geoffrey-young/3D-Printing/models/creality/ender-3-v2/z-drive-helpers/images/IMG_3741.jpg

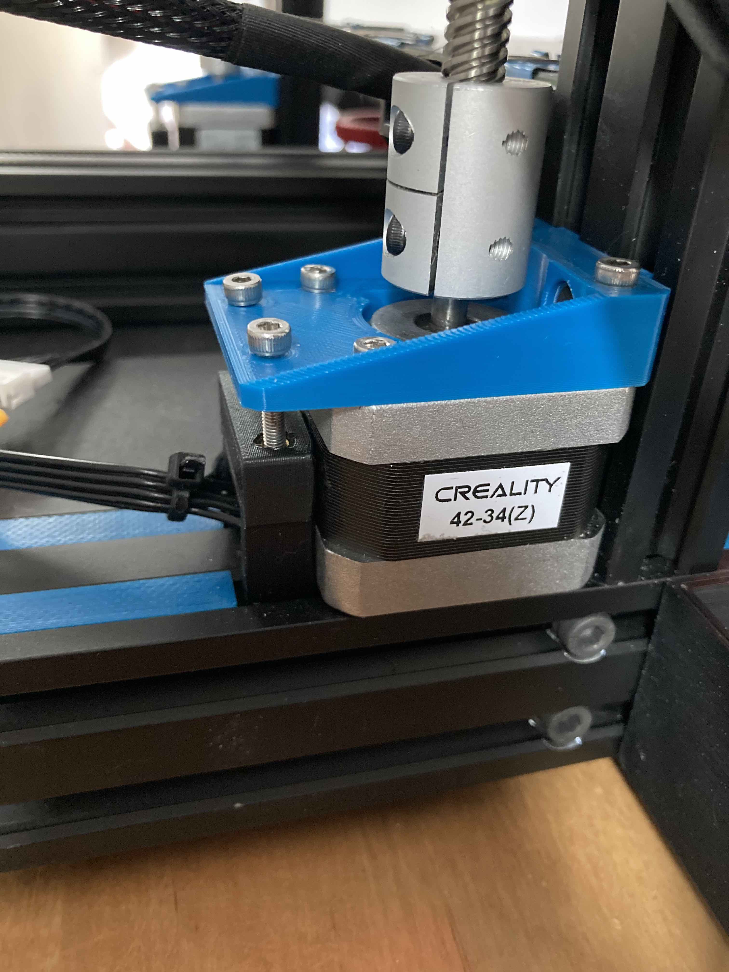
models/creality/ender-3-v2/z-drive-helpers/images/IMG_3741.jpg
