geoffrey-young/3D-Printing/models/creality/ender-3-v2/z-drive-helpers/images/motor.jpg

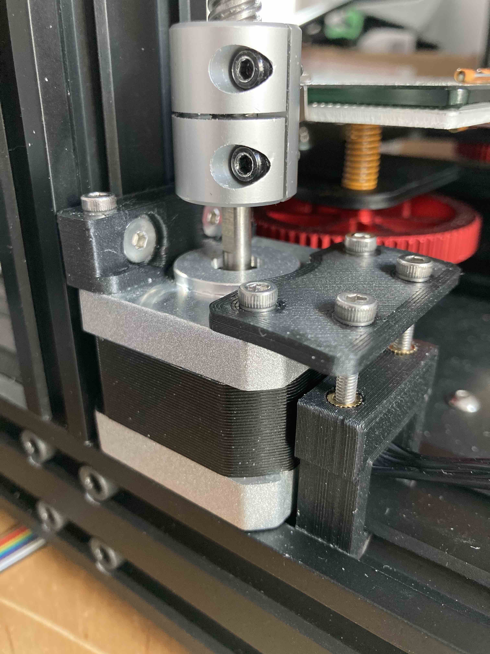
models/creality/ender-3-v2/z-drive-helpers/images/motor.jpg
