geoffrey-young/3D-Printing/models/d20-wall-art/images/IMG_3674.jpg

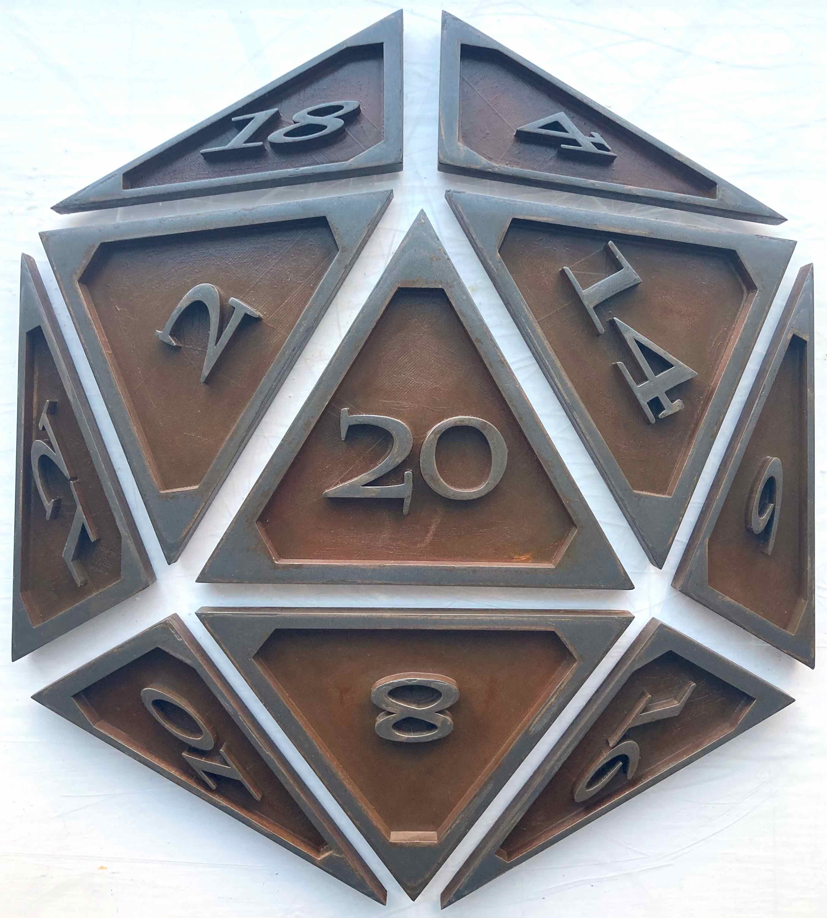
models/d20-wall-art/images/IMG_3674.jpg
