geoffrey-young/3D-Printing/models/d20-wall-art/images/IMG_6126.JPG

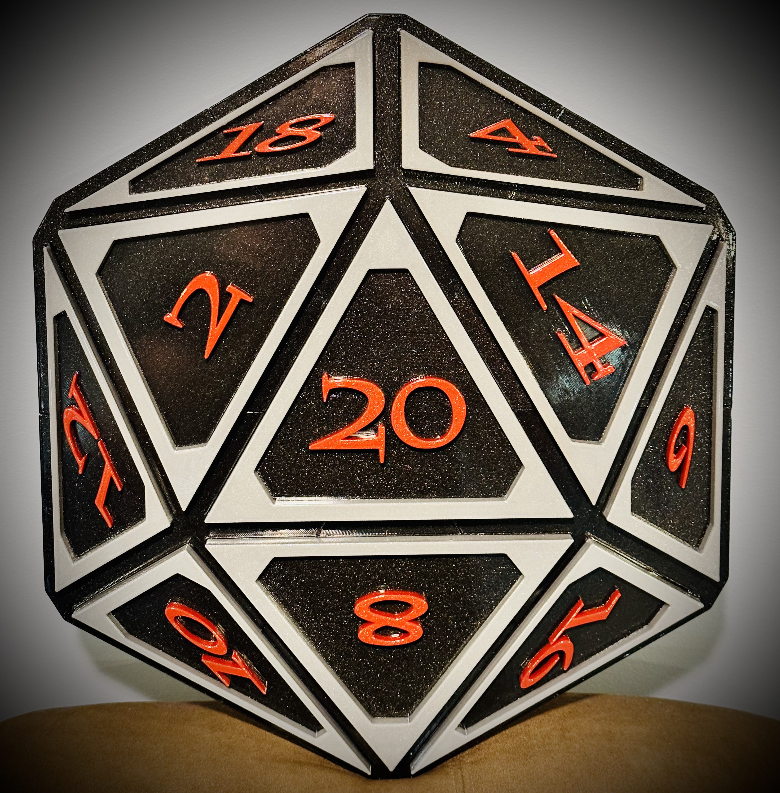
models/d20-wall-art/images/IMG_6126.JPG
