geoffrey-young/3D-Printing/models/voron/2.4/stl/spool-holder/spool-holder.png

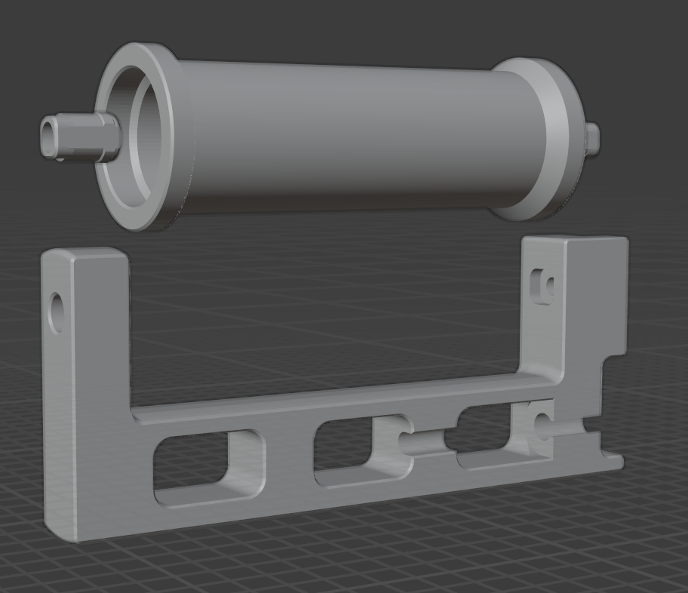
models/voron/2.4/stl/spool-holder/spool-holder.png
