geoffrey-young/3D-Printing/superslicer/voron/sw/ender3_glassbed.png

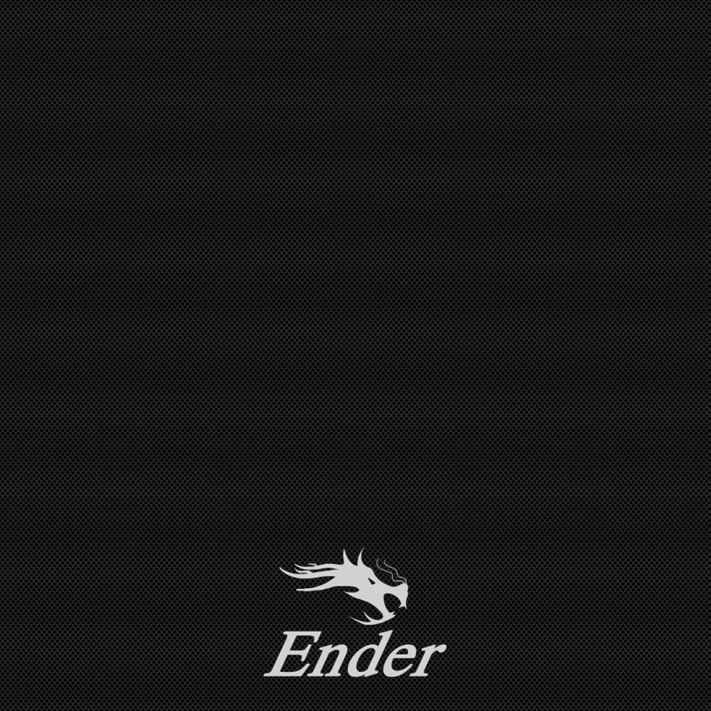
superslicer/voron/sw/ender3_glassbed.png
