geoffrey-young/3D-Printing/models/voron/enderwire/stl/new/y-axis-adxl-mount.stl

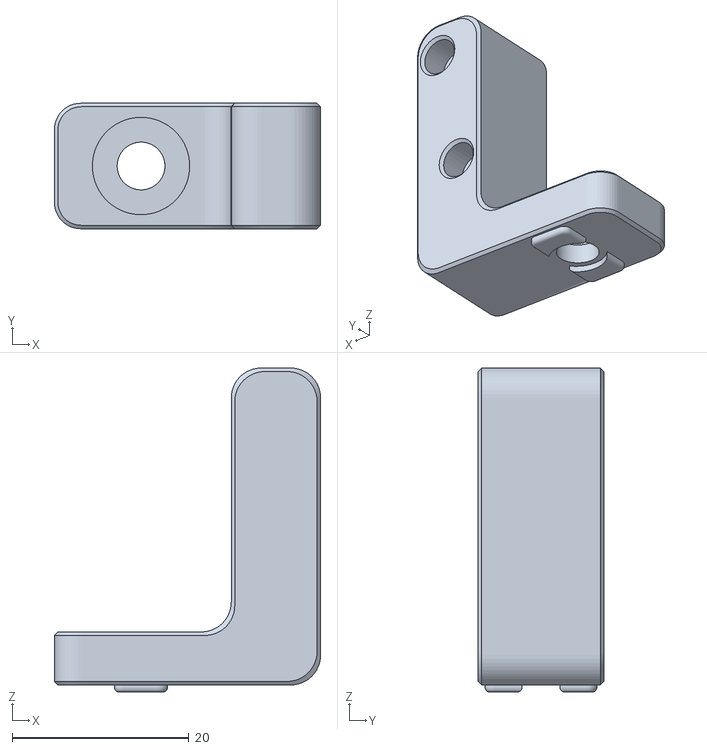
[picture p56: CAD file, 2025-04-14]
models/voron/enderwire/stl/new/y-axis-adxl-mount.stl
30.1 x 14.2 x 36.6
