geoffrey-young/3D-Printing/models/voron/enderwire/stl/replacements/keybak_mount.stl

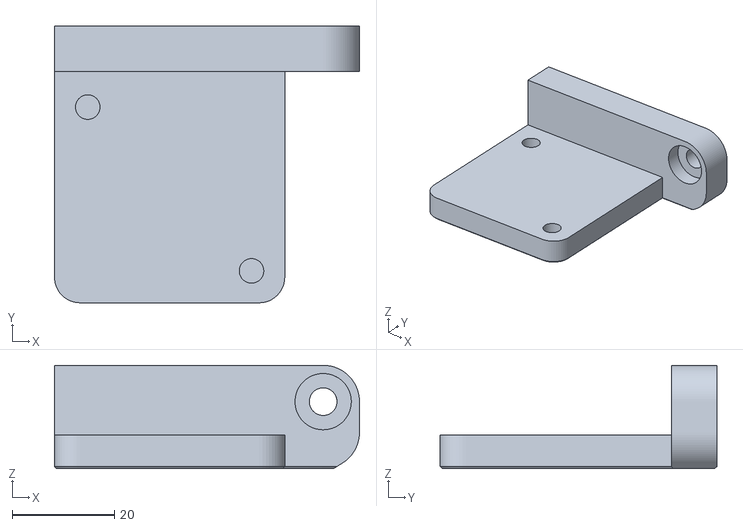
[picture p57: CAD file, 2022-06-13]
models/voron/enderwire/stl/replacements/keybak_mount.stl
59.6 x 54.1 x 20.2
