geoffrey-young/3D-Printing/models/voron/ercf/extender/stl/[a]_10mm-ecas-to-magnet-end_xN.stl

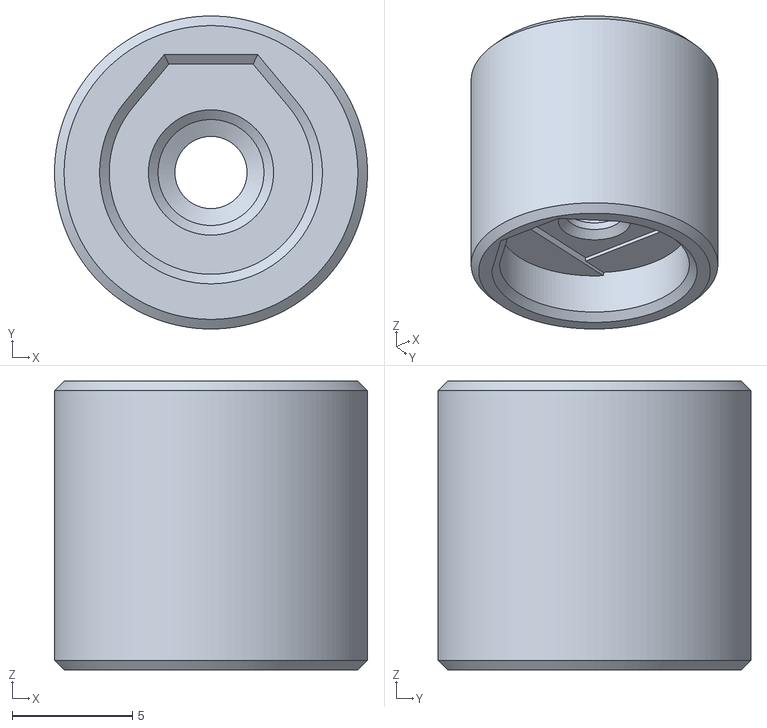
[picture p58: CAD file, 2023-09-01]
models/voron/ercf/extender/stl/[a]_10mm-ecas-to-magnet-end_xN.stl
13.0 x 13.0 x 12.0
