geoffrey-young/3D-Printing/models/voron/ercf/mounts/bridge/stl/bridge-mount-9.stl

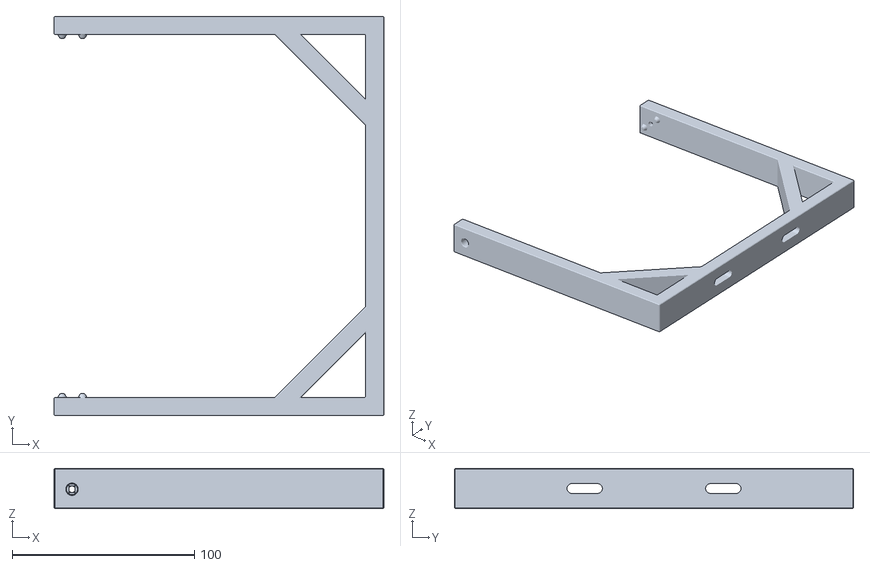
[picture p59: CAD file, 2023-04-11]
models/voron/ercf/mounts/bridge/stl/bridge-mount-9.stl
180.8 x 218.8 x 22.0
