geoffrey-young/3D-Printing/models/voron/ercf/mounts/ercf-french-cleat/stl/frame-6.stl

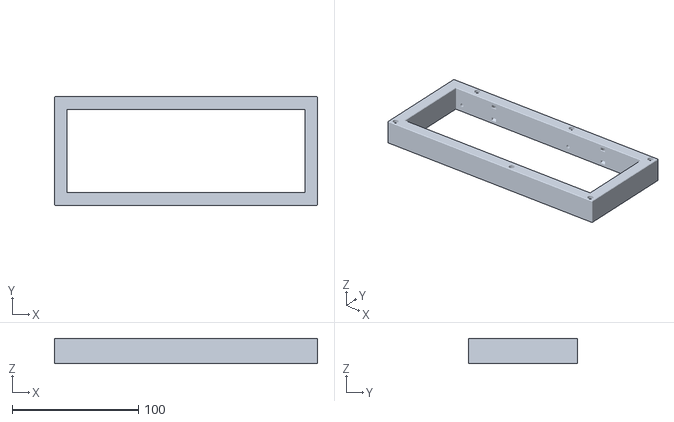
[picture p60: CAD file, 2023-05-19]
models/voron/ercf/mounts/ercf-french-cleat/stl/frame-6.stl
208.0 x 86.0 x 20.0
