geoffrey-young/3D-Printing/models/voron/ercf/random/half-hotends/half-rapido-multicolor.stl

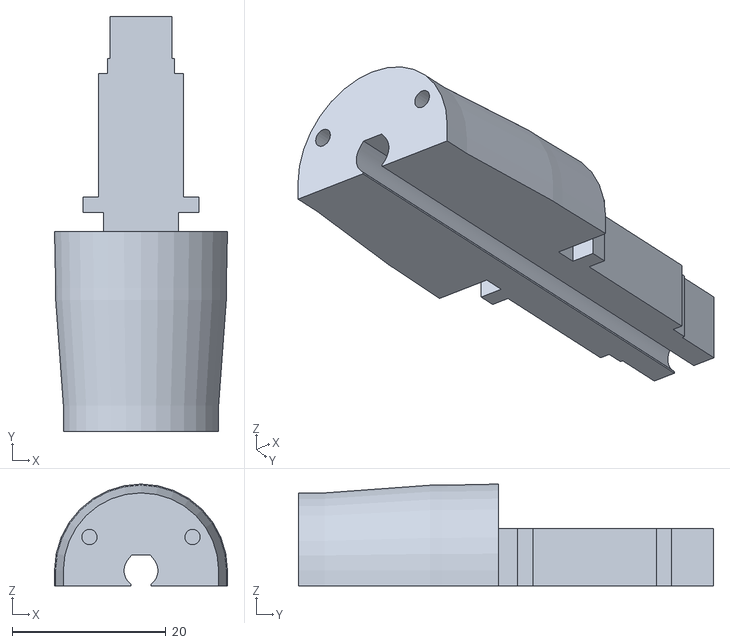
[picture p61: CAD file, 2023-09-01]
models/voron/ercf/random/half-hotends/half-rapido-multicolor.stl
22.5 x 54.0 x 13.3
