geoffrey-young/3D-Printing/models/voron/stealthburner/stl/lgx/cw1/sb-lgx-rear-cw1.stl

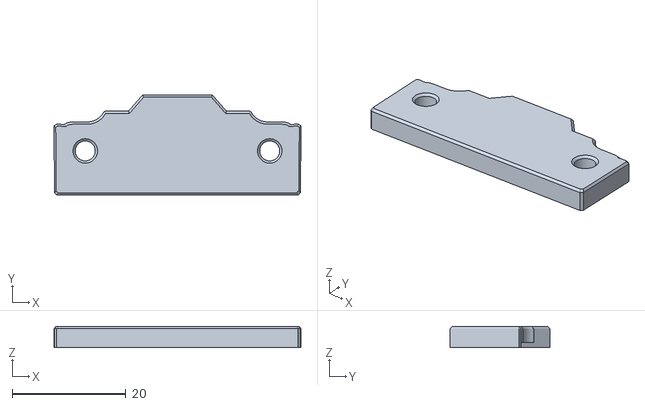
[picture p63: CAD file, 2022-05-10]
models/voron/stealthburner/stl/lgx/cw1/sb-lgx-rear-cw1.stl
43.4 x 17.6 x 3.70
