geoffrey-young/3D-Printing/models/voron/stealthburner/stl/lgx/cw2/sb-lgx-cw2-ercf-v5.stl

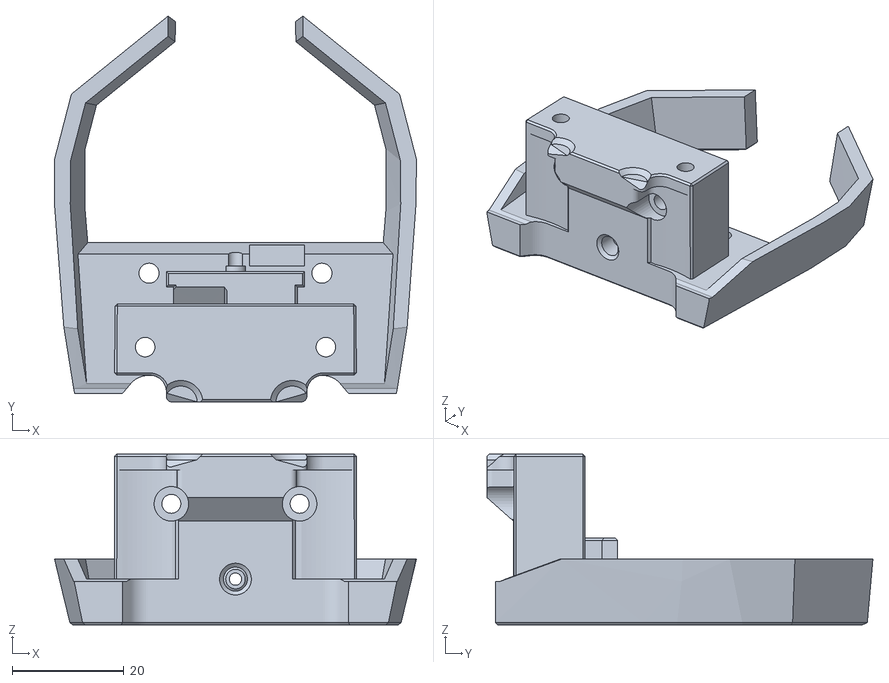
[picture p64: CAD file, 2022-11-18]
models/voron/stealthburner/stl/lgx/cw2/sb-lgx-cw2-ercf-v5.stl
64.9 x 69.2 x 30.6
