geoffrey-young/3D-Printing/models/voron/stealthburner/stl/lgx/sb-lgx-anchor.stl

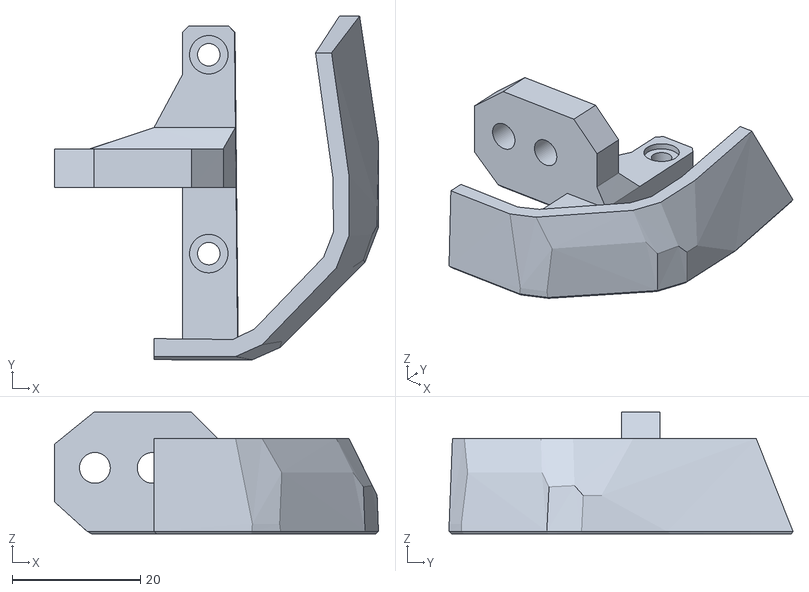
[picture p65: CAD file, 2023-06-22]
models/voron/stealthburner/stl/lgx/sb-lgx-anchor.stl
50.5 x 53.6 x 19.0
