geoffrey-young/3D-Printing/models/voron/stealthburner/stl/sb-official-rapido_filled.stl

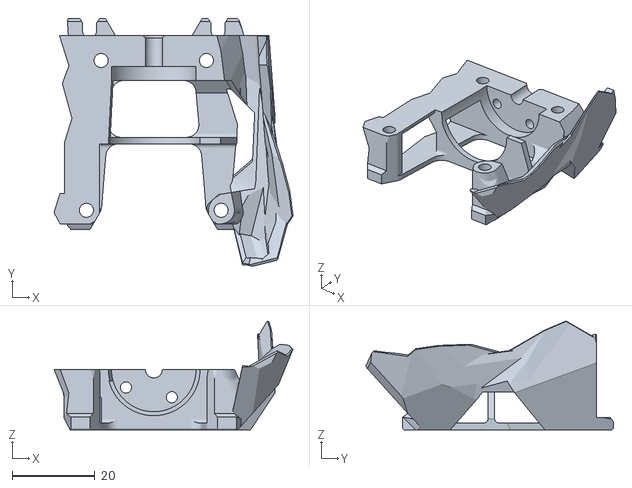
[picture p66: CAD file, 2025-04-14]
models/voron/stealthburner/stl/sb-official-rapido_filled.stl
57.7 x 59.7 x 26.3
