geoffrey-young/3D-Printing/models/voron/tap/r8/short-thick-tap-belt-cover.stl

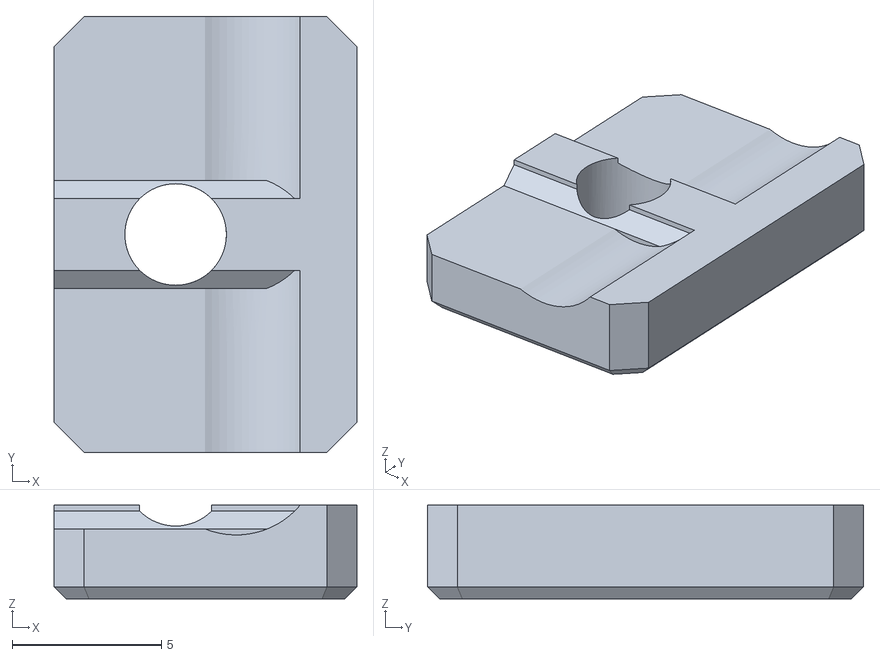
[picture p67: CAD file, 2023-06-17]
models/voron/tap/r8/short-thick-tap-belt-cover.stl
10.1 x 14.6 x 3.14
