geoffrey-young/3D-Printing/models/d20-wall-art/v2/v2-4.stl

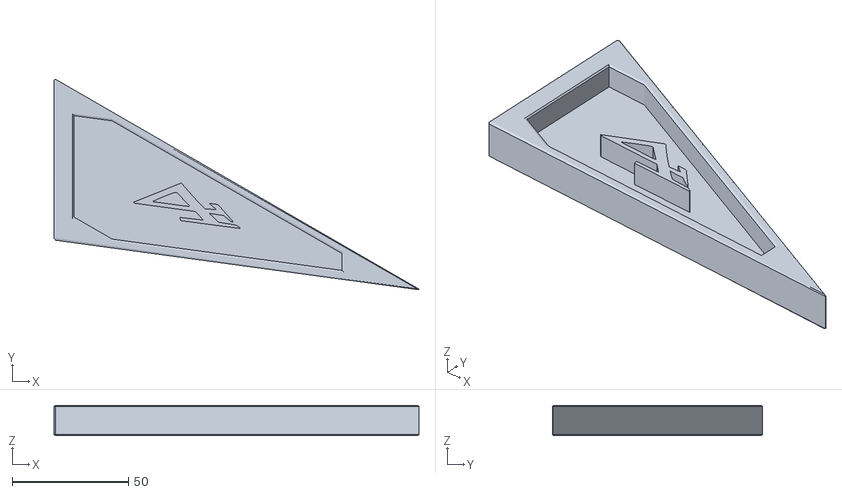
[picture p69: CAD file, 2023-04-01]
models/d20-wall-art/v2/v2-4.stl
157.1 x 90.6 x 13.0
