geoffrey-young/3D-Printing/models/voron/2.4/stl/bofa/filter_access_cover.stl

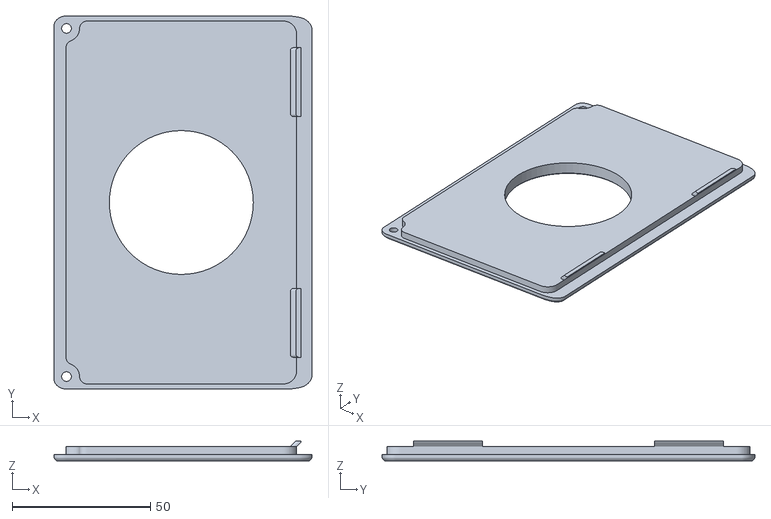
[picture p70: CAD file, 2021-09-11]
models/voron/2.4/stl/bofa/filter_access_cover.stl
93.2 x 134.8 x 7.20
