geoffrey-young/3D-Printing/models/voron/2.4/stl/chains/chain-hold.stl

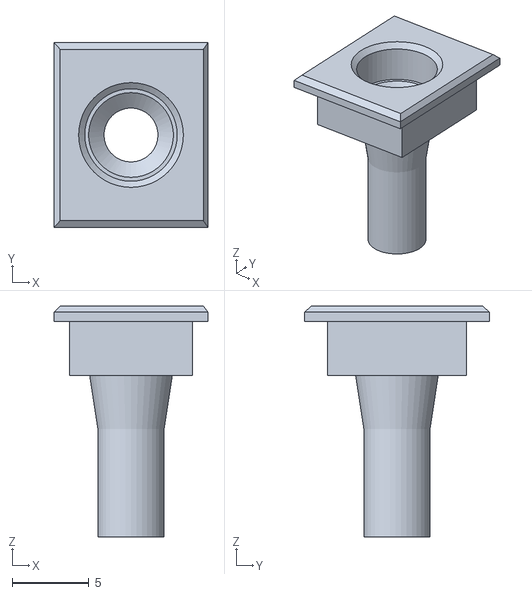
[picture p71: CAD file, 2023-05-01]
models/voron/2.4/stl/chains/chain-hold.stl
10.0 x 12.0 x 15.0
