geoffrey-young/3D-Printing/models/voron/2.4/stl/doors/door_handle_guide.stl

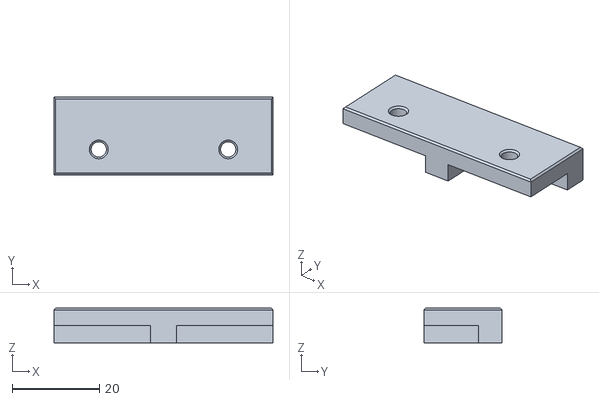
[picture p72: CAD file, 2023-05-01]
models/voron/2.4/stl/doors/door_handle_guide.stl
50.2 x 17.8 x 8.00
