geoffrey-young/3D-Printing/models/voron/2.4/stl/ge5c/ge5c_4_0mm_wider_y_endstop.stl

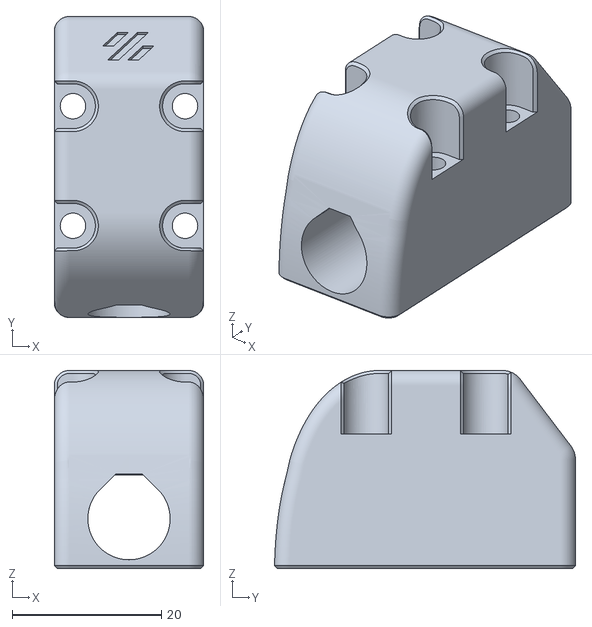
[picture p73: CAD file, 2023-05-01]
models/voron/2.4/stl/ge5c/ge5c_4_0mm_wider_y_endstop.stl
20.0 x 40.3 x 26.5
