geoffrey-young/3D-Printing/models/voron/2.4/stl/other/xy-jst-endstop-pod.stl

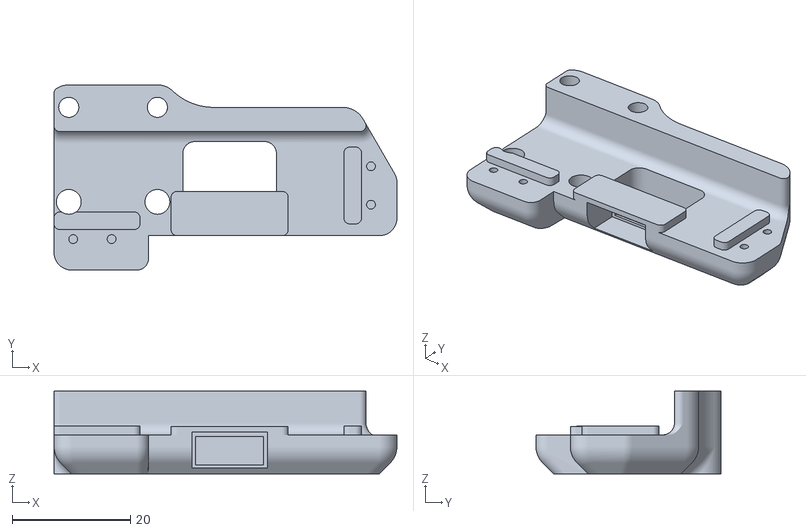
[picture p74: CAD file, 2023-05-01]
models/voron/2.4/stl/other/xy-jst-endstop-pod.stl
58.0 x 31.4 x 14.0
