geoffrey-young/3D-Printing/models/voron/2.4/stl/sb-lgx/lgx-lever-cover.stl

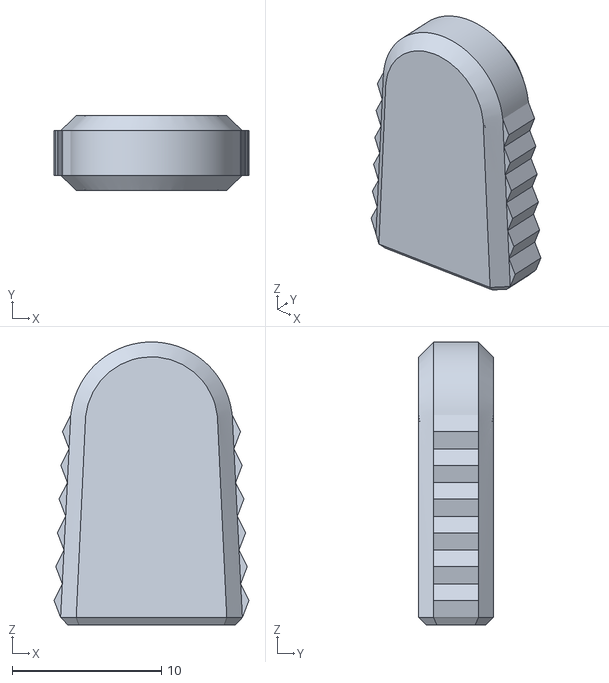
[picture p75: CAD file, 2021-06-12]
models/voron/2.4/stl/sb-lgx/lgx-lever-cover.stl
13.1 x 5.00 x 19.0
