geoffrey-young/3D-Printing/models/voron/2.4/stl/skirts/left-rear.stl

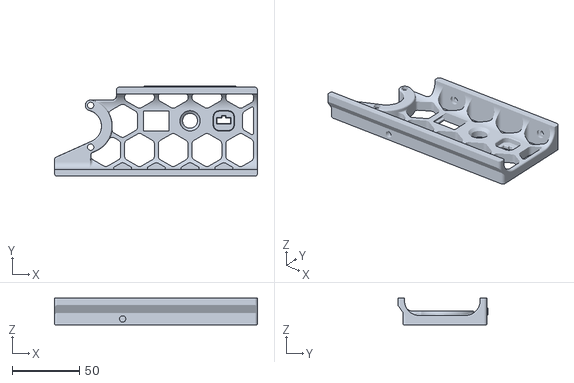
[picture p76: CAD file, 2023-05-01]
models/voron/2.4/stl/skirts/left-rear.stl
150.5 x 67.0 x 20.0
