geoffrey-young/3D-Printing/models/voron/2.4/stl/spool-holder/bearing_mount-x2.stl

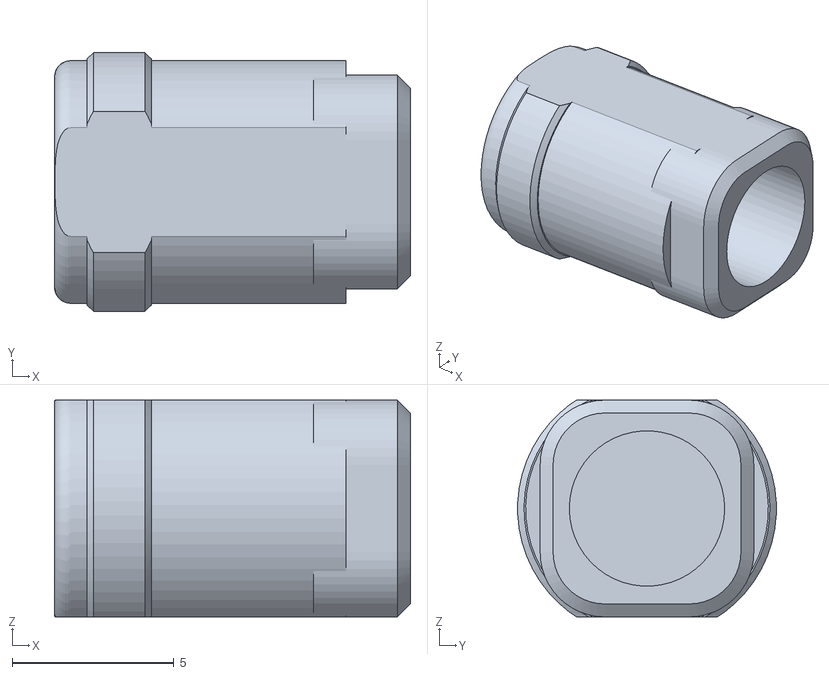
[picture p77: CAD file, 2021-06-15]
models/voron/2.4/stl/spool-holder/bearing_mount-x2.stl
11.0 x 7.99 x 6.70
