geoffrey-young/3D-Printing/models/voron/2.4/stl/tap/55mm-a__Tap_Center_r8.stl

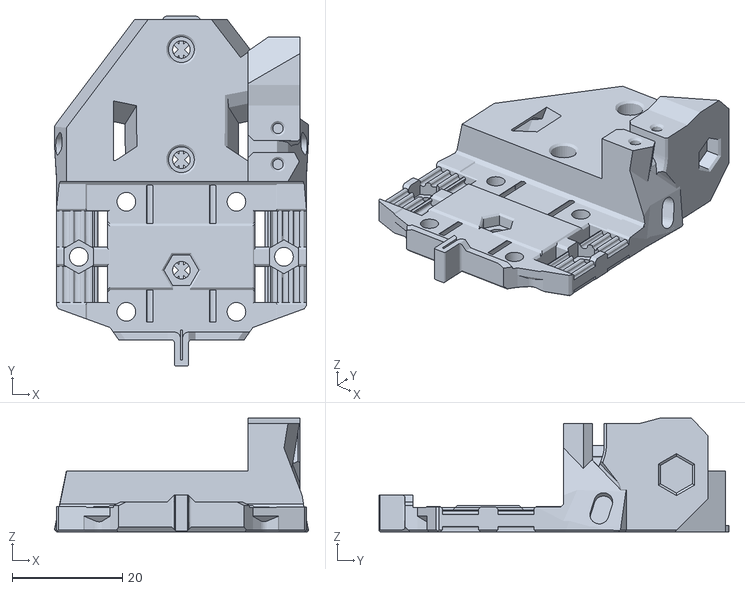
[picture p78: CAD file, 2023-06-17]
models/voron/2.4/stl/tap/55mm-a__Tap_Center_r8.stl
46.2 x 63.6 x 20.7
