geoffrey-young/3D-Printing/models/voron/enderwire/stl/new/long-klicky-mount.stl

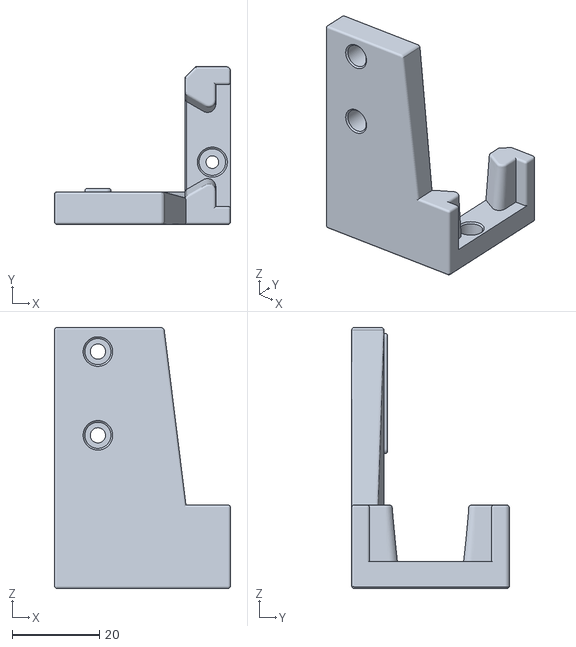
[picture p79: CAD file, 2023-12-30]
models/voron/enderwire/stl/new/long-klicky-mount.stl
40.5 x 36.3 x 60.0
