geoffrey-young/3D-Printing/models/voron/enderwire/stl/replacements/[a]_y_axis_ls_mount.stl

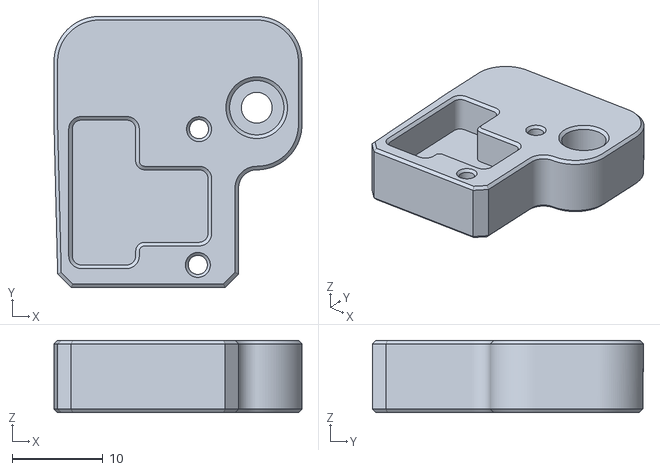
[picture p80: CAD file, 2022-06-13]
models/voron/enderwire/stl/replacements/[a]_y_axis_ls_mount.stl
27.4 x 30.0 x 8.00
