geoffrey-young/3D-Printing/models/voron/ercf/extender/stl/10mm-extender-6.stl

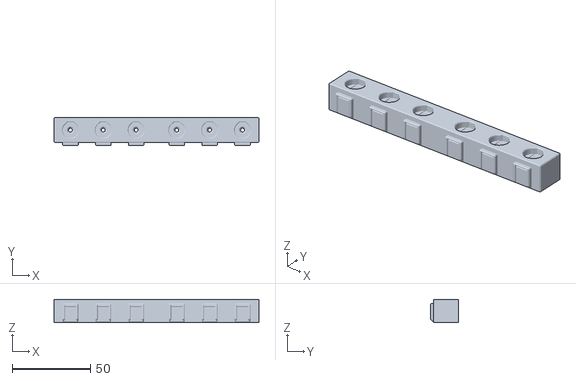
[picture p81: CAD file, 2023-09-01]
models/voron/ercf/extender/stl/10mm-extender-6.stl
131.0 x 18.0 x 15.0
