geoffrey-young/3D-Printing/models/voron/ercf/mounts/bridge/stl/bridge-9.stl

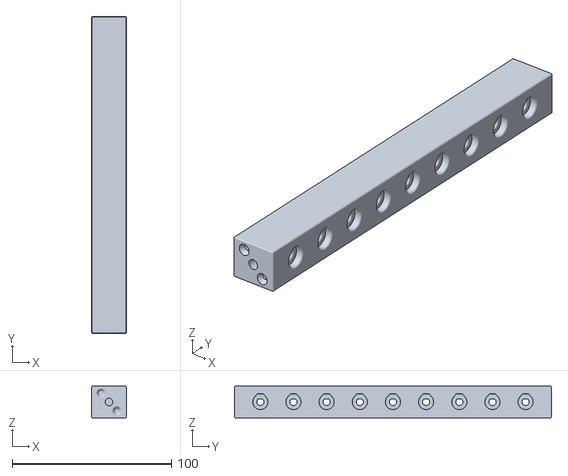
[picture p82: CAD file, 2023-04-11]
models/voron/ercf/mounts/bridge/stl/bridge-9.stl
22.0 x 198.8 x 20.0
