geoffrey-young/3D-Printing/models/voron/ercf/mounts/ercf-french-cleat/stl/wall-mount-6.stl

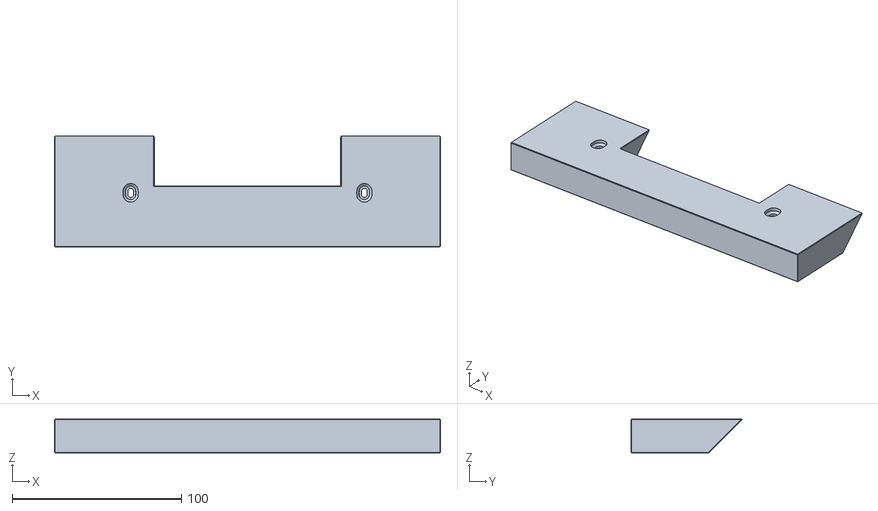
[picture p83: CAD file, 2023-05-19]
models/voron/ercf/mounts/ercf-french-cleat/stl/wall-mount-6.stl
228.0 x 65.7 x 20.0
