geoffrey-young/3D-Printing/models/voron/ercf/random/filament-measure.stl

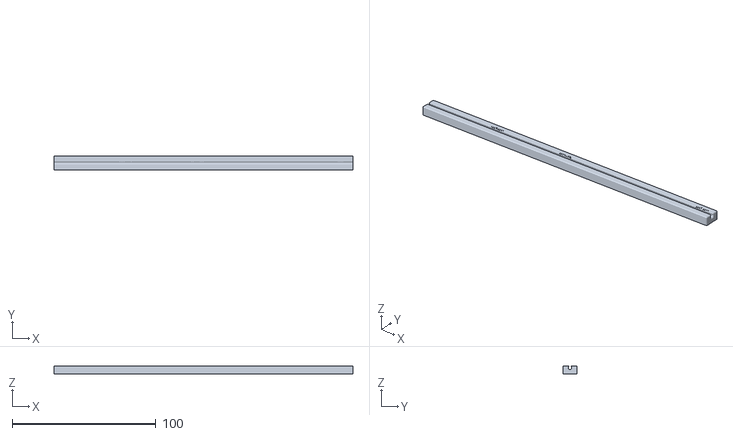
[picture p84: CAD file, 2023-06-12]
models/voron/ercf/random/filament-measure.stl
208.0 x 10.0 x 5.80
