geoffrey-young/3D-Printing/models/voron/ercf/random/half-hotends/half-dragon-multicolor.stl

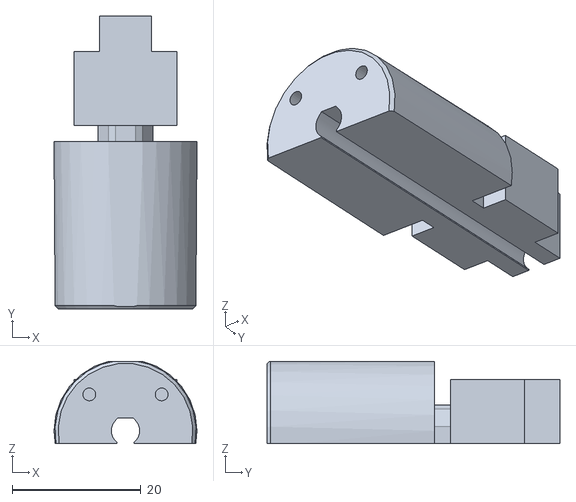
[picture p85: CAD file, 2023-09-01]
models/voron/ercf/random/half-hotends/half-dragon-multicolor.stl
22.2 x 45.5 x 12.8
