geoffrey-young/3D-Printing/models/voron/ercf/upside-down-numbers/stl/3.stl

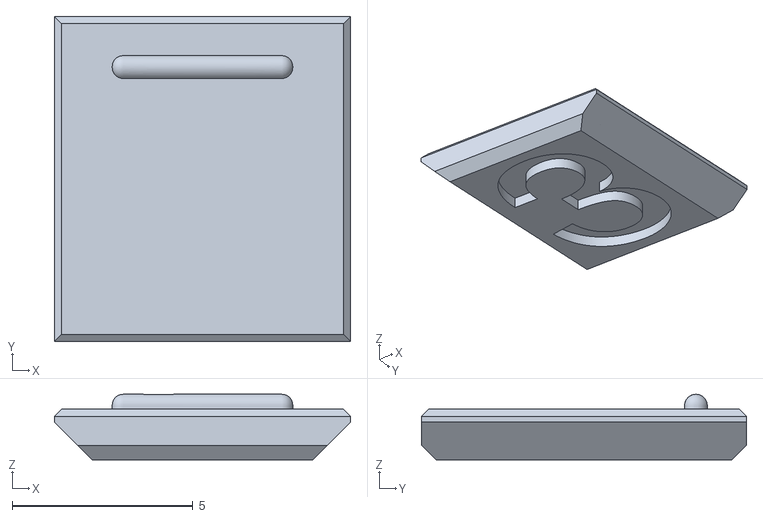
[picture p86: CAD file, 2022-11-07]
models/voron/ercf/upside-down-numbers/stl/3.stl
8.20 x 9.00 x 1.82
