geoffrey-young/3D-Printing/models/voron/stealthburner/stl/lgx/cw1/sb-lgx-front-cw1.stl

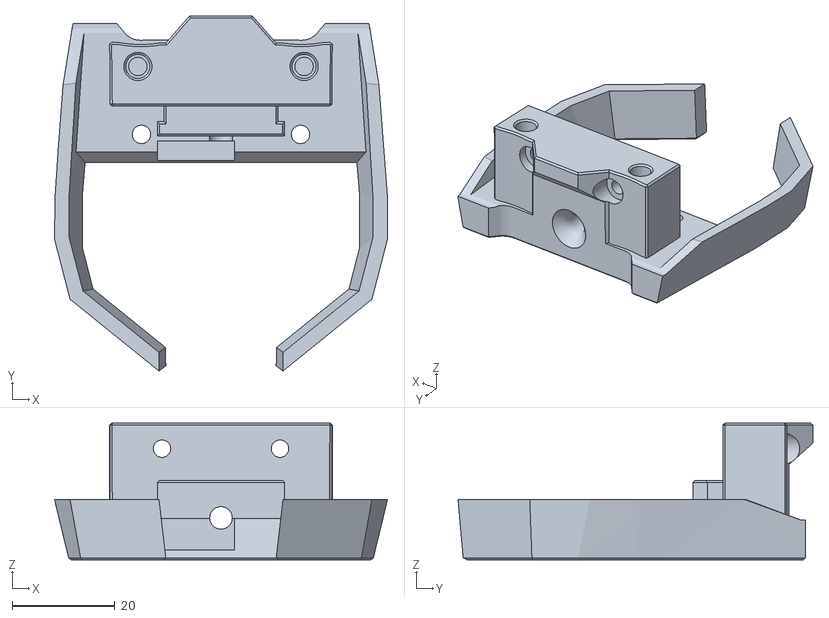
[picture p87: CAD file, 2022-03-18]
models/voron/stealthburner/stl/lgx/cw1/sb-lgx-front-cw1.stl
64.9 x 69.2 x 26.7
