geoffrey-young/3D-Printing/models/voron/stealthburner/stl/lgx/sb-lgx-cover.stl

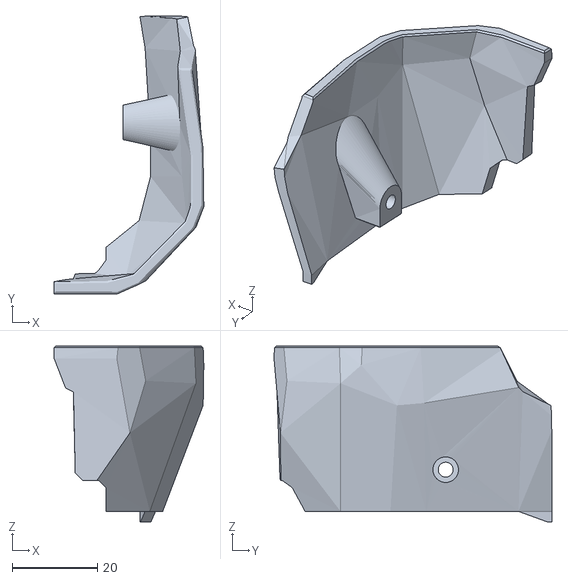
[picture p88: CAD file, 2022-05-10]
models/voron/stealthburner/stl/lgx/sb-lgx-cover.stl
35.2 x 65.3 x 41.3
