geoffrey-young/3D-Printing/models/creality/ender-3-v2/z-drive-helpers/stl/z-axis-mount-with-bracket.stl

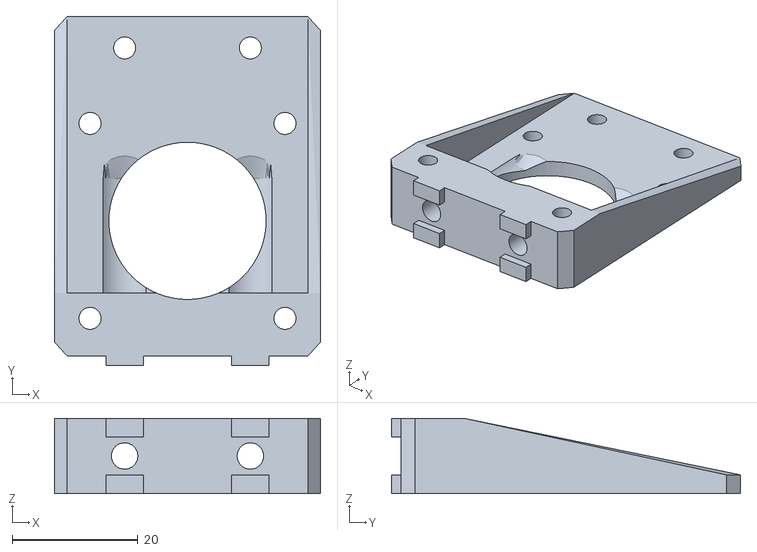
[picture p90: CAD file, 2021-06-09]
models/creality/ender-3-v2/z-drive-helpers/stl/z-axis-mount-with-bracket.stl
42.3 x 55.5 x 12.0
