geoffrey-young/3D-Printing/models/d20-wall-art/v2/base/v2-base-3.stl

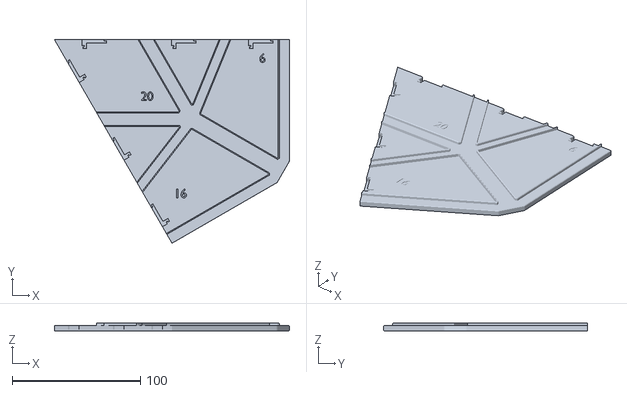
[picture p91: CAD file, 2023-04-01]
models/d20-wall-art/v2/base/v2-base-3.stl
183.5 x 158.9 x 6.00
