geoffrey-young/3D-Printing/models/d20-wall-art/v2/guides/v2-left-guide.stl

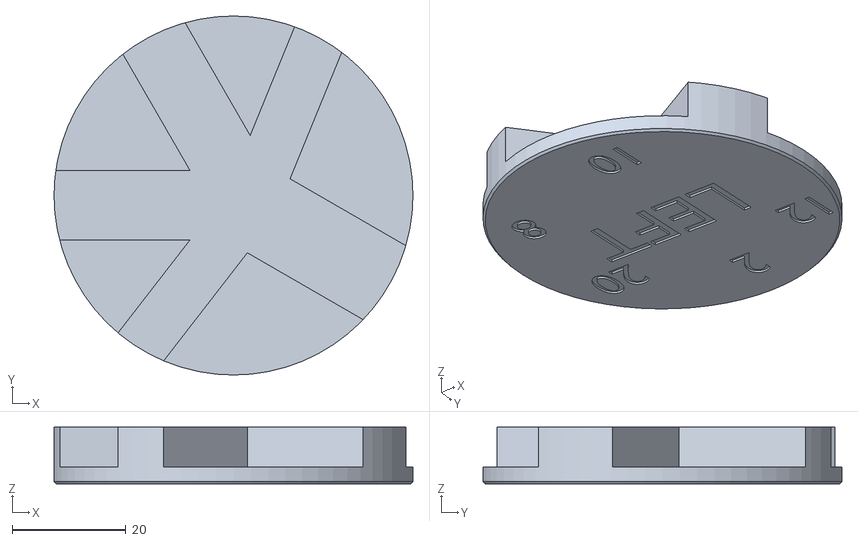
[picture p92: CAD file, 2023-04-01]
models/d20-wall-art/v2/guides/v2-left-guide.stl
63.0 x 63.0 x 10.0
