geoffrey-young/3D-Printing/models/d20-wall-art/v2/v2-14.stl

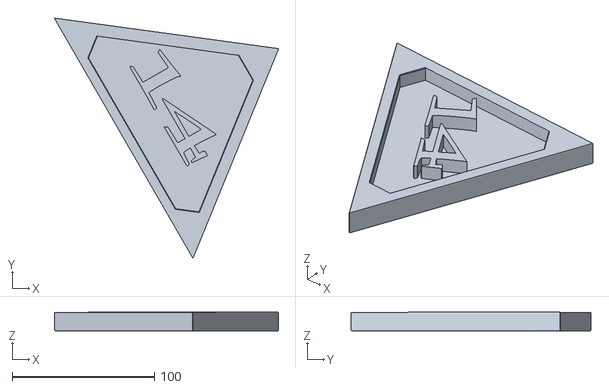
[picture p93: CAD file, 2023-04-01]
models/d20-wall-art/v2/v2-14.stl
157.4 x 168.5 x 13.0
