geoffrey-young/3D-Printing/models/voron/2.4/stl/bofa/exhaust_filter_housing.stl

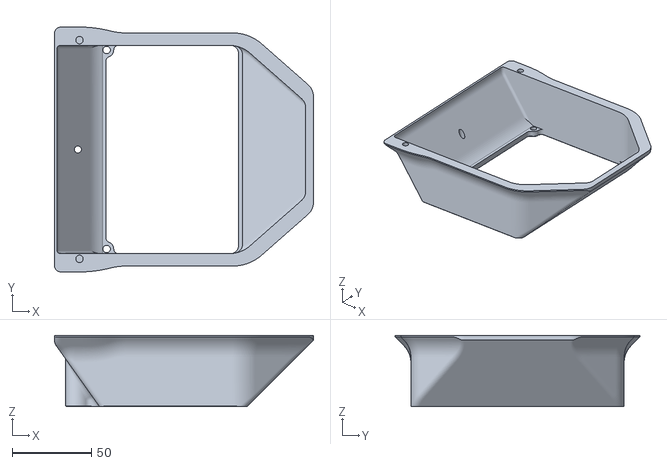
[picture p94: CAD file, 2021-09-11]
models/voron/2.4/stl/bofa/exhaust_filter_housing.stl
163.7 x 154.8 x 45.0
