geoffrey-young/3D-Printing/models/voron/2.4/stl/chains/z_chain_end-outer.stl

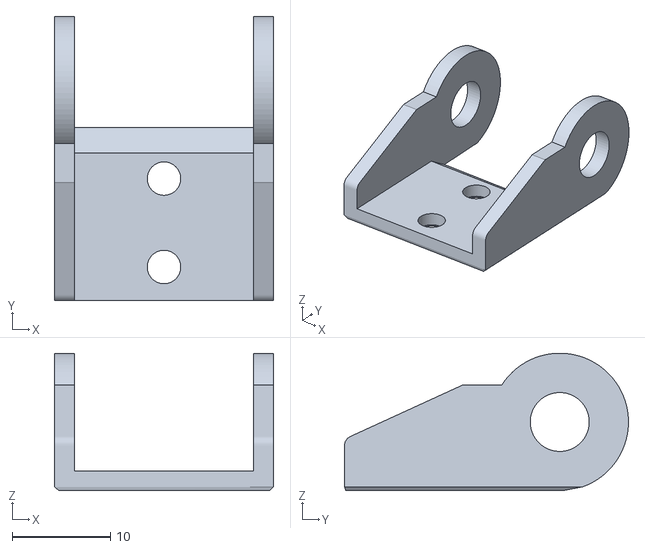
[picture p95: CAD file, 2022-04-29]
models/voron/2.4/stl/chains/z_chain_end-outer.stl
22.3 x 28.9 x 14.0
