geoffrey-young/3D-Printing/models/voron/2.4/stl/doors/door_handles_ab.stl

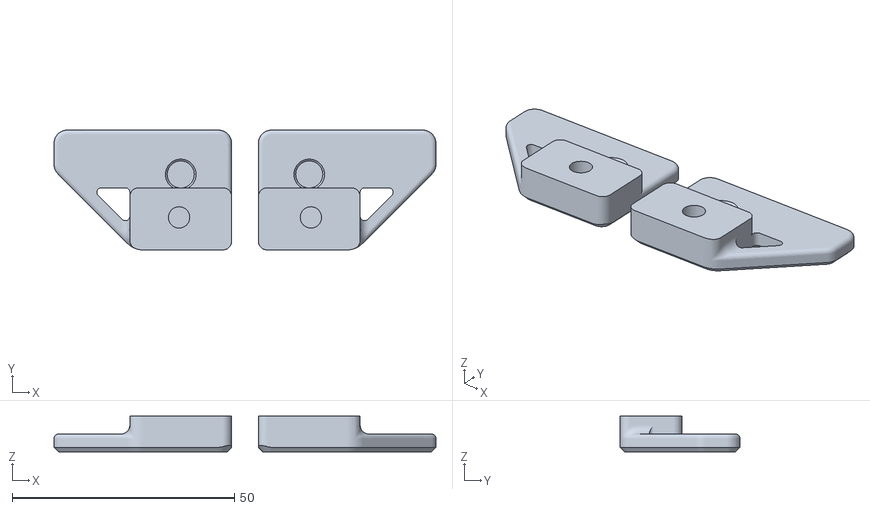
[picture p96: CAD file, 2023-05-01]
models/voron/2.4/stl/doors/door_handles_ab.stl
86.0 x 27.0 x 8.00
