geoffrey-young/3D-Printing/models/voron/2.4/stl/other/bottom-panel-anchor.stl

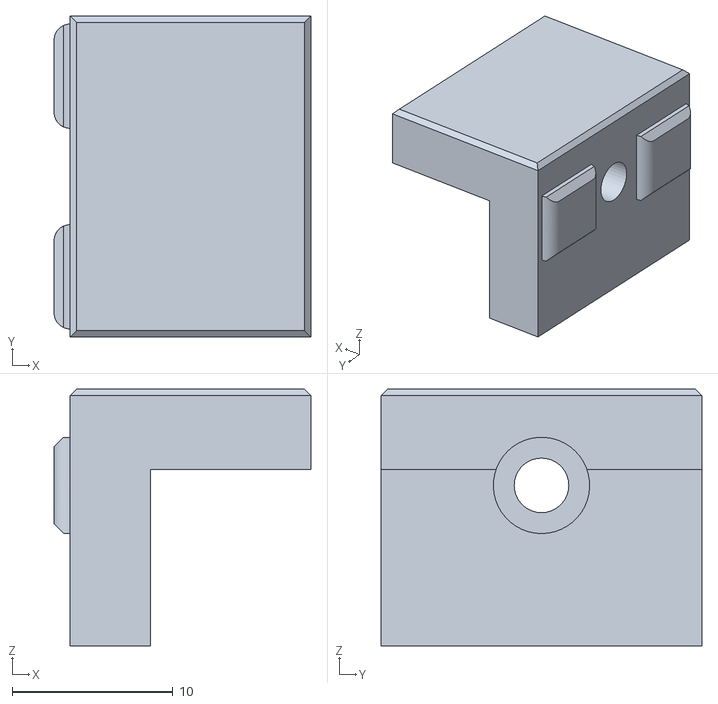
[picture p97: CAD file, 2023-05-01]
models/voron/2.4/stl/other/bottom-panel-anchor.stl
16.0 x 20.0 x 16.0
