geoffrey-young/3D-Printing/models/voron/2.4/stl/spool-holder/roller.stl

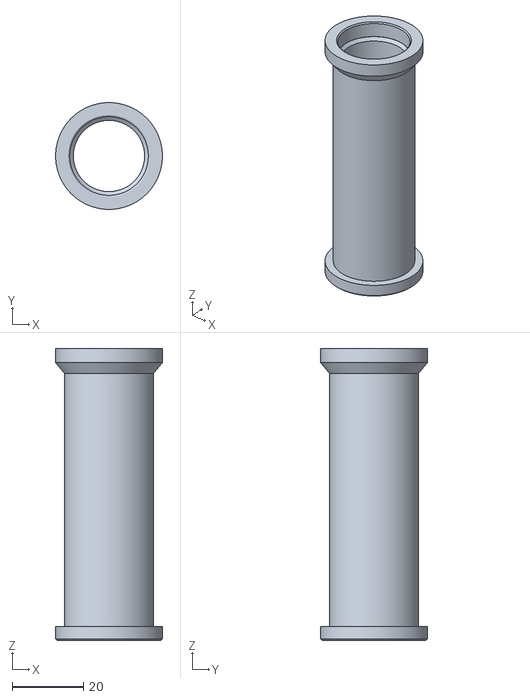
[picture p98: CAD file, 2021-06-15]
models/voron/2.4/stl/spool-holder/roller.stl
30.0 x 30.0 x 82.0
