geoffrey-young/3D-Printing/models/voron/2.4/stl/tap/short_tap_belt_cover_r8_x2.stl

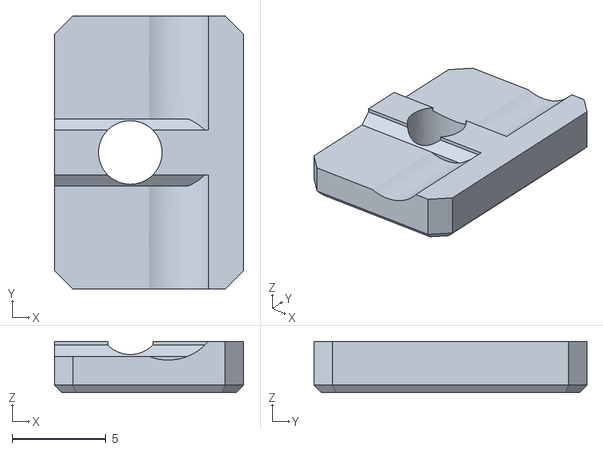
[picture p99: CAD file, 2023-06-05]
models/voron/2.4/stl/tap/short_tap_belt_cover_r8_x2.stl
10.1 x 14.6 x 2.74
