geoffrey-young/3D-Printing/models/voron/enderwire/stl/new/stealthbowden-body.stl

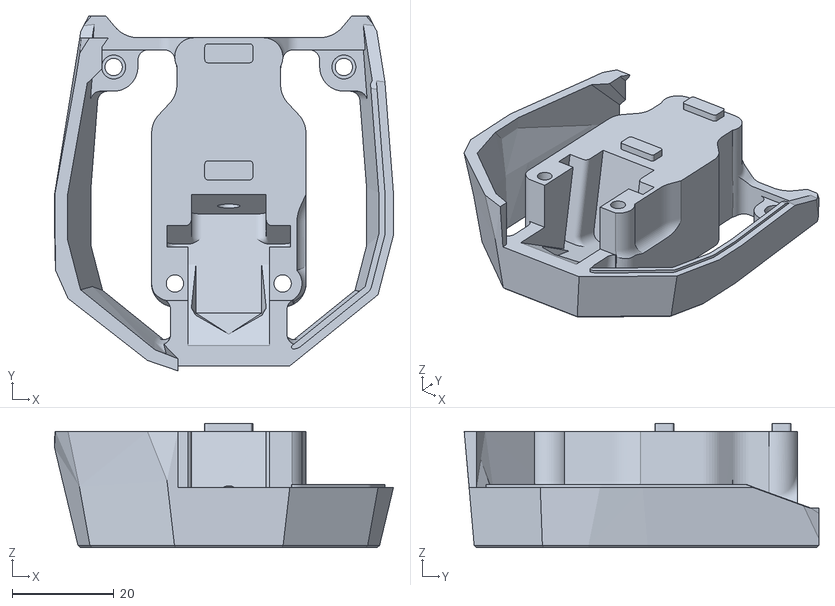
[picture p100: CAD file, 2022-06-13]
models/voron/enderwire/stl/new/stealthbowden-body.stl
66.6 x 69.7 x 24.4
