geoffrey-young/3D-Printing/models/voron/enderwire/stl/replacements/grill_rear_middle.stl

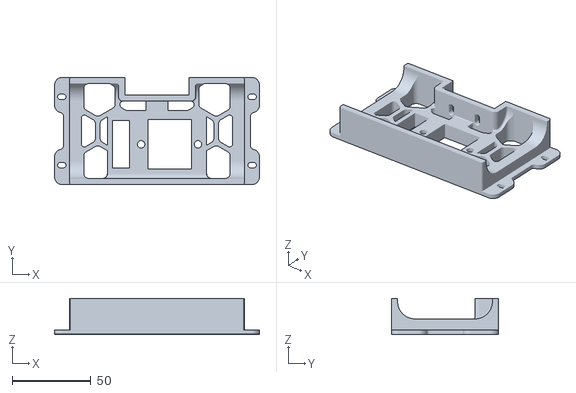
[picture p101: CAD file, 2022-06-13]
models/voron/enderwire/stl/replacements/grill_rear_middle.stl
129.8 x 68.0 x 23.0
