geoffrey-young/3D-Printing/models/voron/ercf/extender/stl/10mm-extender-9.stl

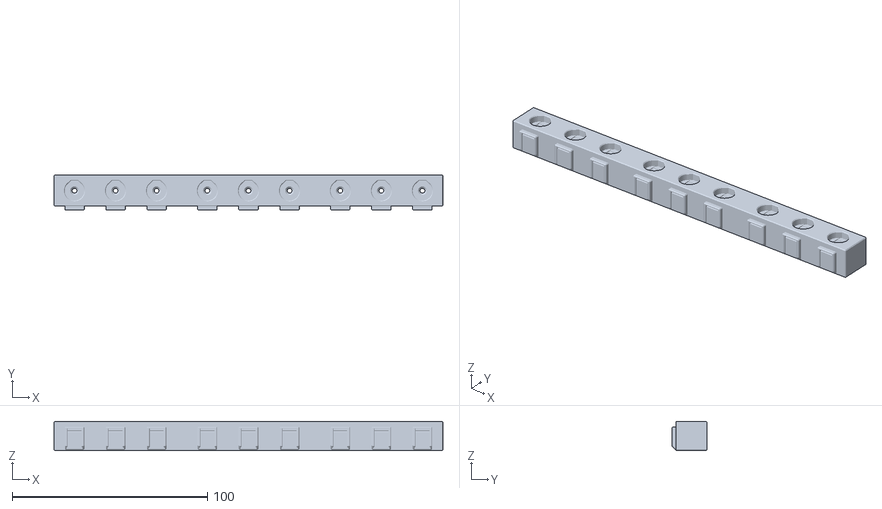
[picture p102: CAD file, 2023-09-01]
models/voron/ercf/extender/stl/10mm-extender-9.stl
199.0 x 18.0 x 15.0
