geoffrey-young/3D-Printing/models/voron/ercf/mounts/bridge/stl/bridge-mount-12.stl

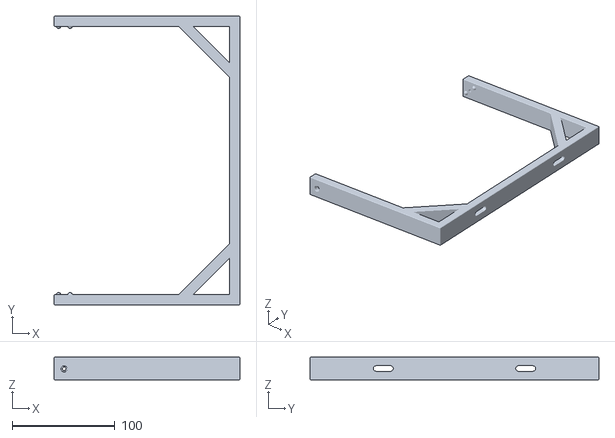
[picture p103: CAD file, 2023-04-11]
models/voron/ercf/mounts/bridge/stl/bridge-mount-12.stl
180.8 x 281.2 x 22.0
