geoffrey-young/3D-Printing/models/voron/ercf/mounts/ercf-french-cleat/stl/frame-12.stl

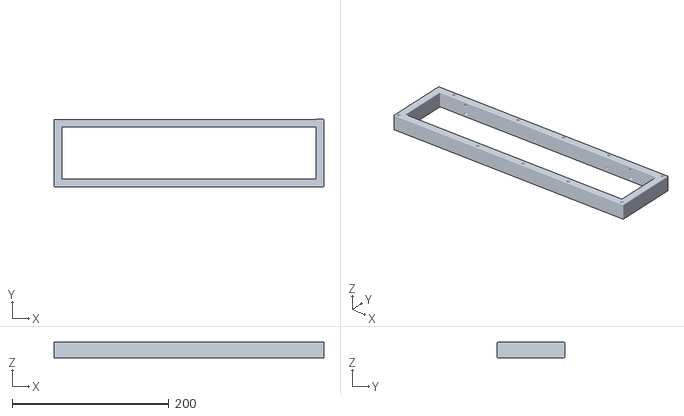
[picture p104: CAD file, 2023-02-27]
models/voron/ercf/mounts/ercf-french-cleat/stl/frame-12.stl
344.0 x 86.0 x 20.0
