geoffrey-young/3D-Printing/models/voron/ercf/random/spring-hold.stl

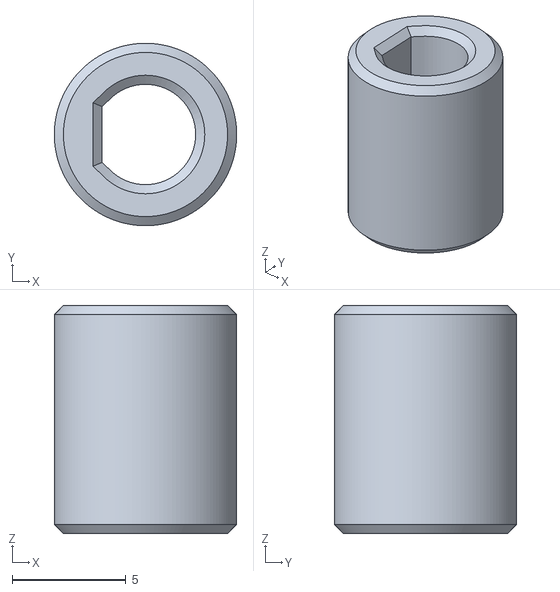
[picture p105: CAD file, 2023-04-11]
models/voron/ercf/random/spring-hold.stl
8.00 x 8.00 x 10.0
