geoffrey-young/3D-Printing/models/creality/ender-3-v2/z-drive-helpers/stl/top-bracket.stl

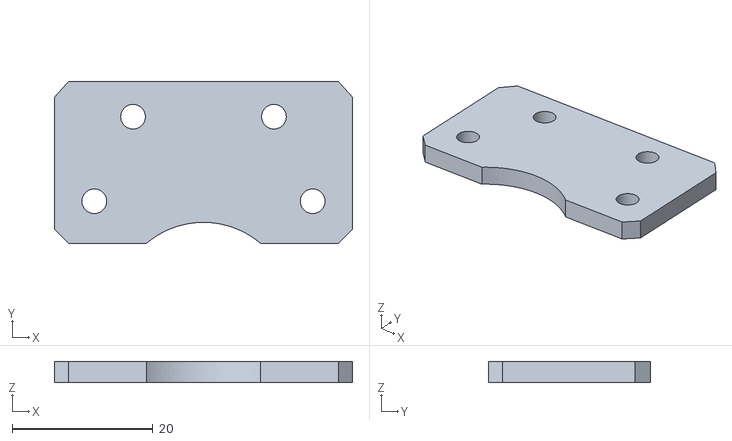
[picture p106: CAD file, 2021-06-09]
models/creality/ender-3-v2/z-drive-helpers/stl/top-bracket.stl
42.3 x 23.0 x 3.00
