geoffrey-young/3D-Printing/models/d20-wall-art/v2/base/v2-base-clip-x18.stl

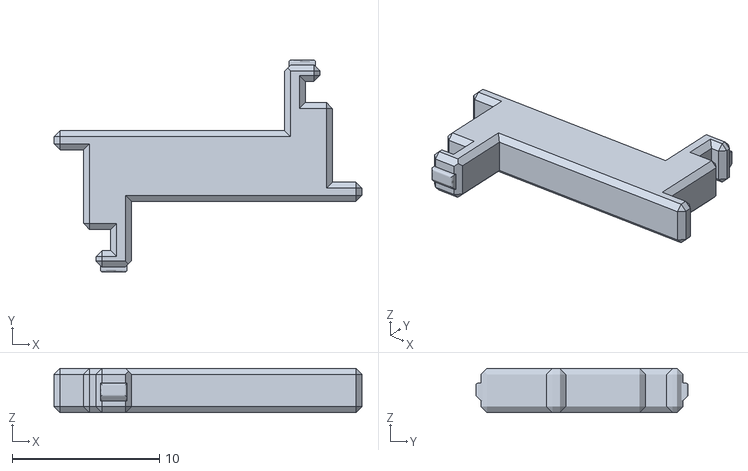
[picture p107: CAD file, 2023-04-01]
models/d20-wall-art/v2/base/v2-base-clip-x18.stl
20.9 x 14.4 x 3.00
