geoffrey-young/3D-Printing/models/d20-wall-art/v2/v2-2.stl

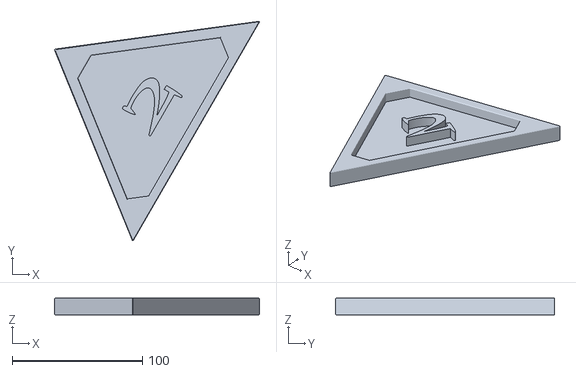
[picture p108: CAD file, 2023-04-01]
models/d20-wall-art/v2/v2-2.stl
157.1 x 168.1 x 13.0
