geoffrey-young/3D-Printing/models/voron/2.4/stl/bofa/bowden_coupling.stl

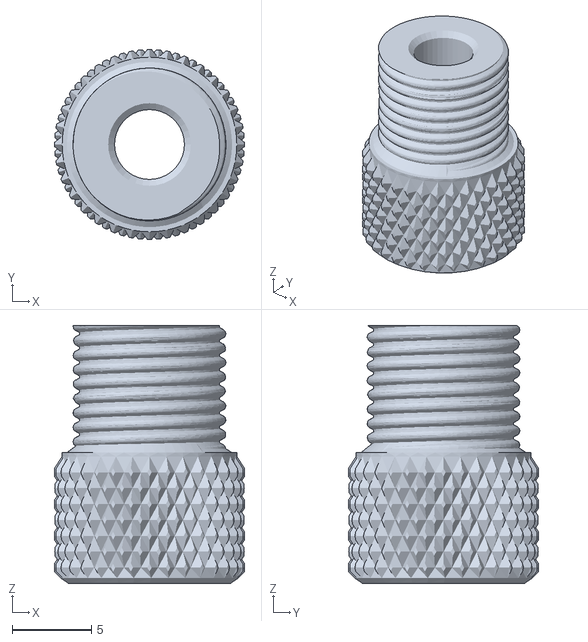
[picture p109: CAD file, 2021-09-11]
models/voron/2.4/stl/bofa/bowden_coupling.stl
12.0 x 12.0 x 16.2
