geoffrey-young/3D-Printing/models/voron/2.4/stl/chains/z_chain_end-inner.stl

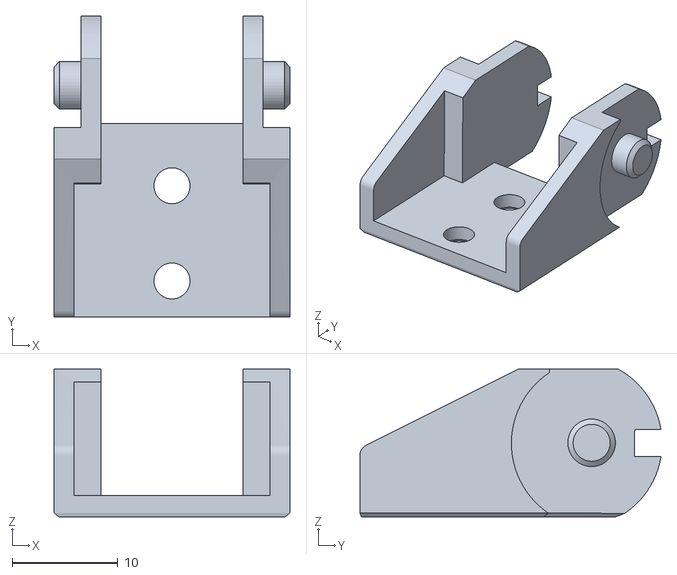
[picture p110: CAD file, 2022-04-29]
models/voron/2.4/stl/chains/z_chain_end-inner.stl
22.3 x 28.5 x 14.0
