geoffrey-young/3D-Printing/models/voron/2.4/stl/doors/hinge_mount.stl

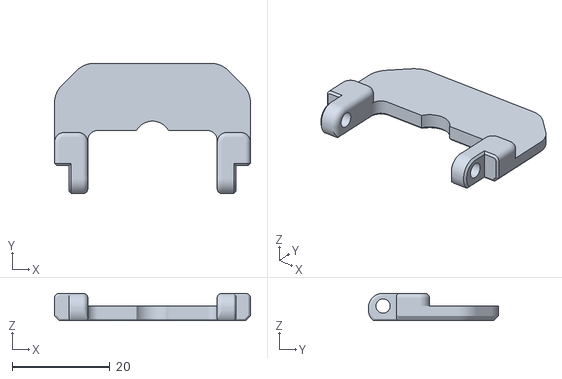
[picture p111: CAD file, 2023-05-01]
models/voron/2.4/stl/doors/hinge_mount.stl
40.0 x 26.6 x 5.60
