geoffrey-young/3D-Printing/models/voron/enderwire/stl/new/tl-filament-sensor-bracket.stl

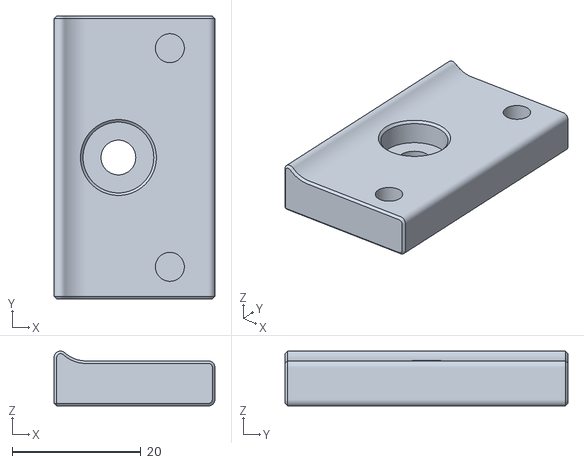
[picture p112: CAD file, 2022-06-13]
models/voron/enderwire/stl/new/tl-filament-sensor-bracket.stl
25.0 x 44.0 x 8.53
