geoffrey-young/3D-Printing/models/voron/enderwire/stl/replacements/grill_rear_right.stl

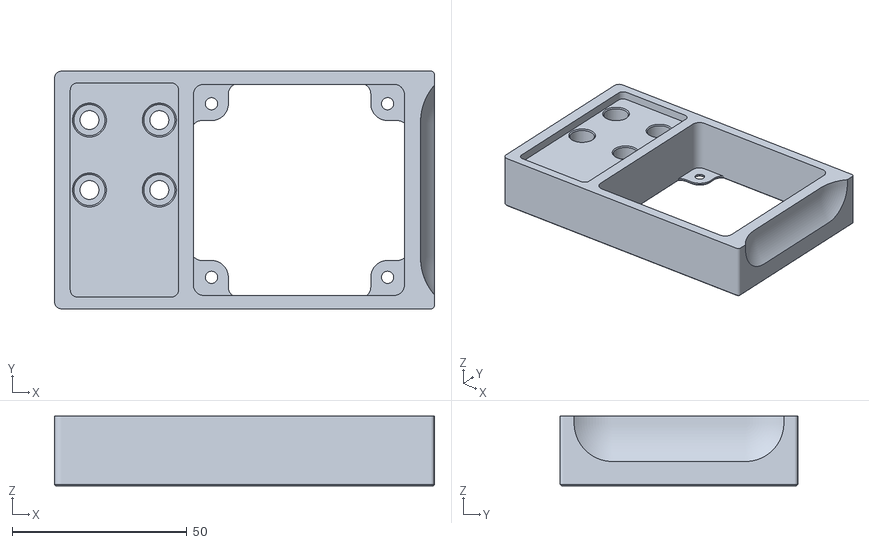
[picture p113: CAD file, 2022-06-13]
models/voron/enderwire/stl/replacements/grill_rear_right.stl
108.7 x 68.0 x 20.0
