geoffrey-young/3D-Printing/models/voron/ercf/extender/stl/10mm-extender-12.stl

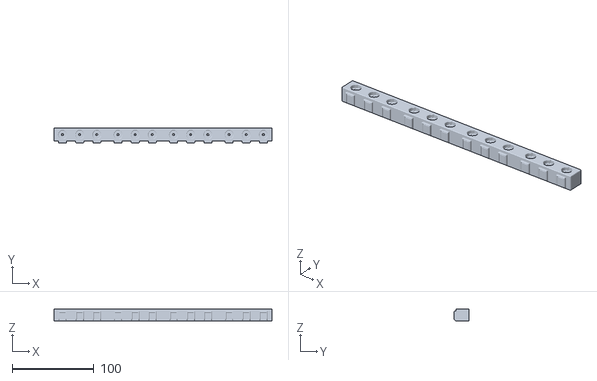
[picture p114: CAD file, 2023-09-01]
models/voron/ercf/extender/stl/10mm-extender-12.stl
267.0 x 18.0 x 15.0
