geoffrey-young/3D-Printing/models/voron/ercf/mounts/bridge/stl/bridge-6.stl

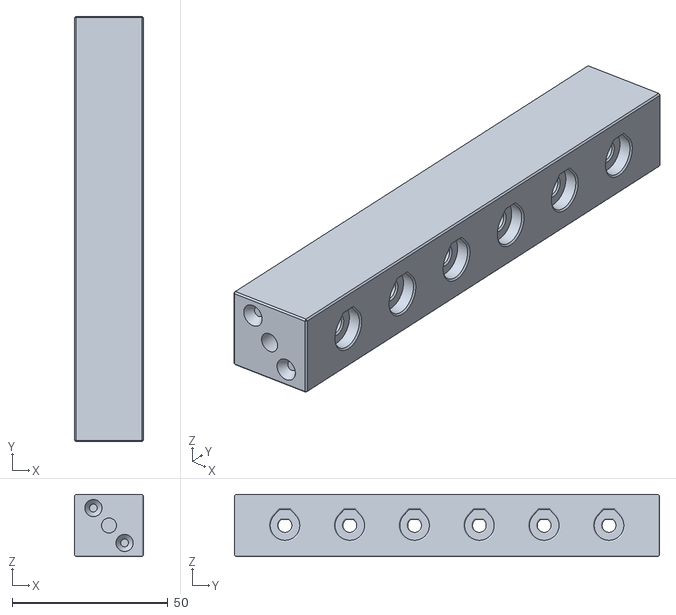
[picture p115: CAD file, 2023-04-11]
models/voron/ercf/mounts/bridge/stl/bridge-6.stl
22.0 x 136.4 x 20.0
