geoffrey-young/3D-Printing/models/voron/ercf/mounts/ercf-french-cleat/stl/wall-mount-12.stl

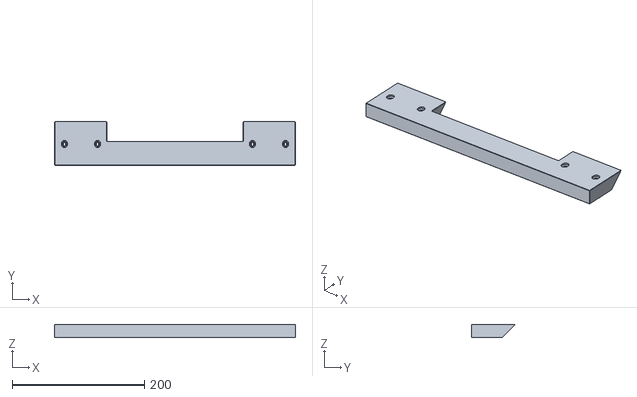
[picture p116: CAD file, 2023-02-27]
models/voron/ercf/mounts/ercf-french-cleat/stl/wall-mount-12.stl
364.0 x 65.7 x 20.0
