geoffrey-young/3D-Printing/models/voron/ercf/random/nema14-motor-arm-metal-80T.stl

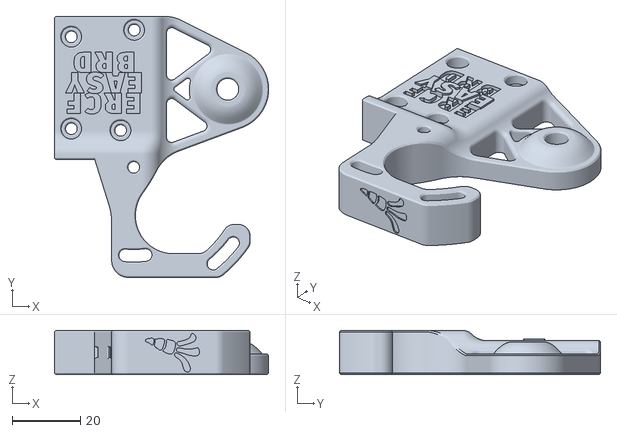
[picture p117: CAD file, 2023-01-15]
models/voron/ercf/random/nema14-motor-arm-metal-80T.stl
63.0 x 76.7 x 13.0
