geoffrey-young/3D-Printing/models/d20-wall-art/v2/guides/v2-left-guide-mmu.stl

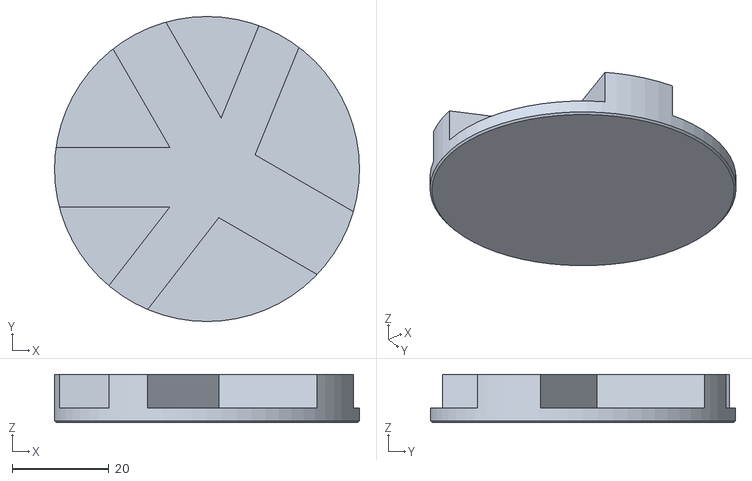
[picture p119: CAD file, 2023-04-01]
models/d20-wall-art/v2/guides/v2-left-guide-mmu.stl
63.0 x 63.0 x 10.0
