geoffrey-young/3D-Printing/models/voron/2.4/stl/chains/xy_chain_end-outer.stl

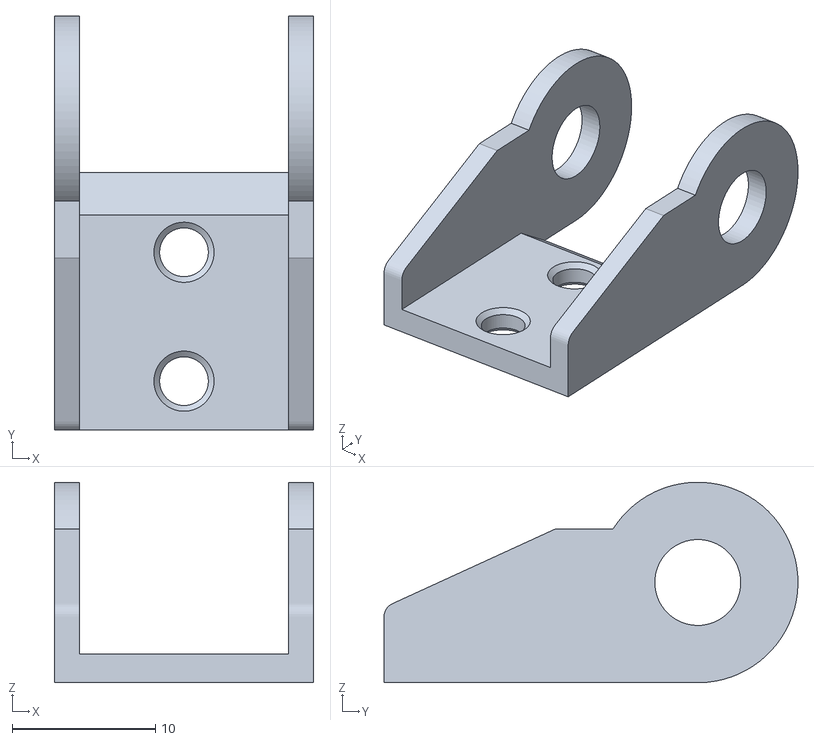
[picture p120: CAD file, 2021-07-02]
models/voron/2.4/stl/chains/xy_chain_end-outer.stl
18.1 x 28.9 x 14.0
