geoffrey-young/3D-Printing/models/voron/enderwire/stl/new/extruder-inlet.stl

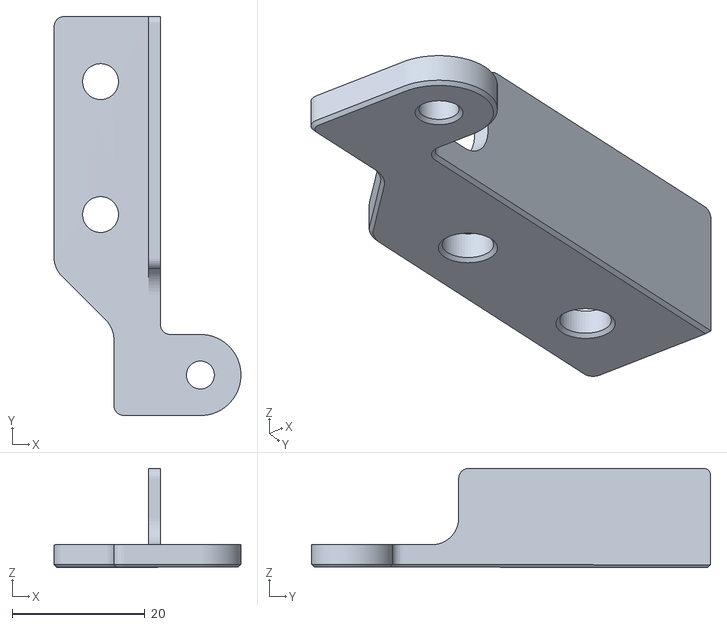
[picture p121: CAD file, 2022-06-13]
models/voron/enderwire/stl/new/extruder-inlet.stl
28.1 x 60.0 x 14.9
