geoffrey-young/3D-Printing/models/voron/enderwire/stl/replacements/[a]_xz_cable_cover.stl

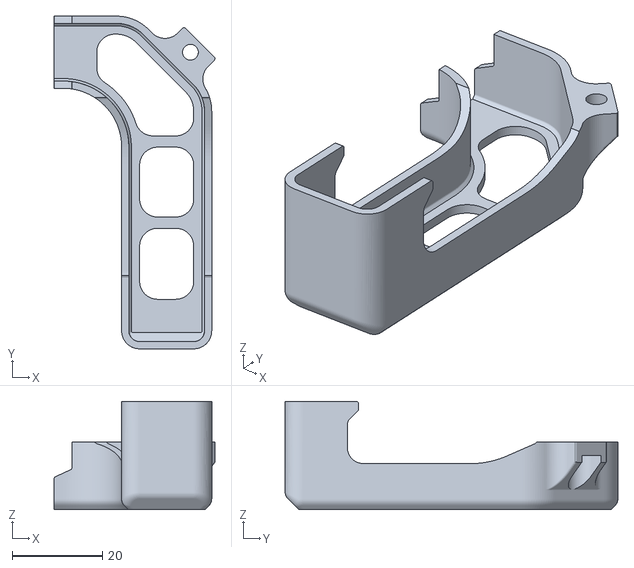
[picture p122: CAD file, 2022-06-13]
models/voron/enderwire/stl/replacements/[a]_xz_cable_cover.stl
35.7 x 73.8 x 24.0
