geoffrey-young/3D-Printing/models/voron/ercf/extender/stl/magnet-test-blocks.stl

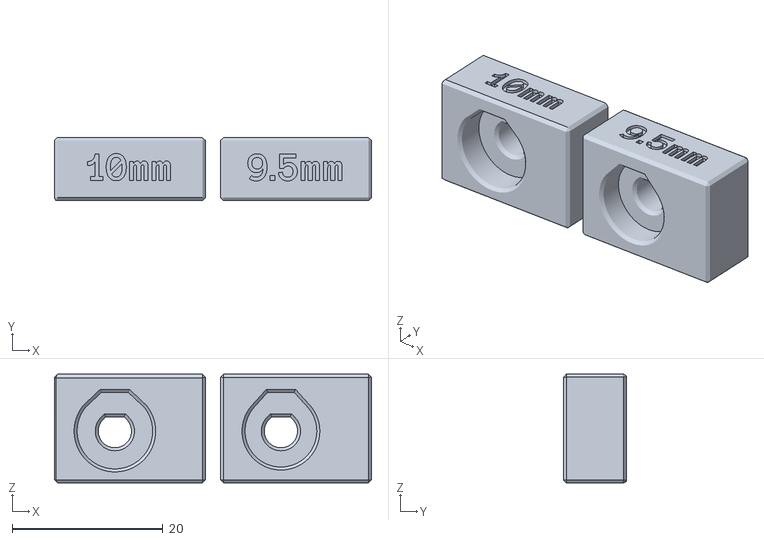
[picture p123: CAD file, 2023-09-01]
models/voron/ercf/extender/stl/magnet-test-blocks.stl
42.0 x 8.40 x 14.4
