geoffrey-young/3D-Printing/models/voron/ercf/mounts/bridge/stl/bridge-12.stl

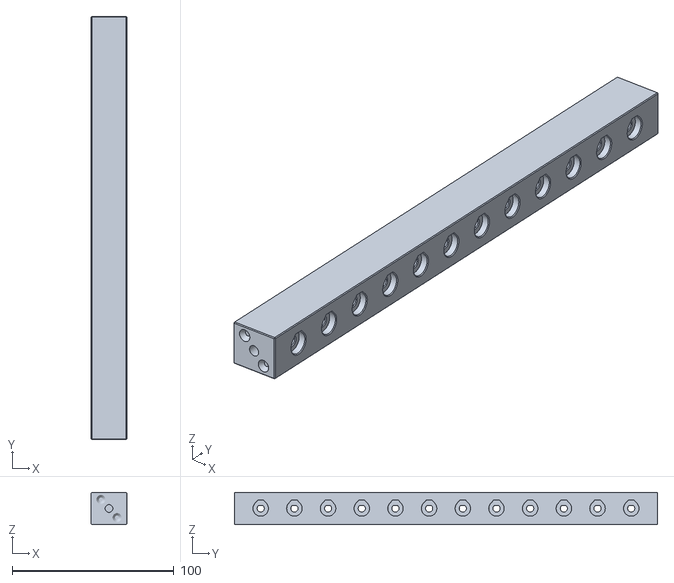
[picture p124: CAD file, 2023-04-11]
models/voron/ercf/mounts/bridge/stl/bridge-12.stl
22.0 x 261.2 x 20.0
