geoffrey-young/3D-Printing/models/voron/ercf/mounts/ercf-french-cleat/stl/frame-9.stl

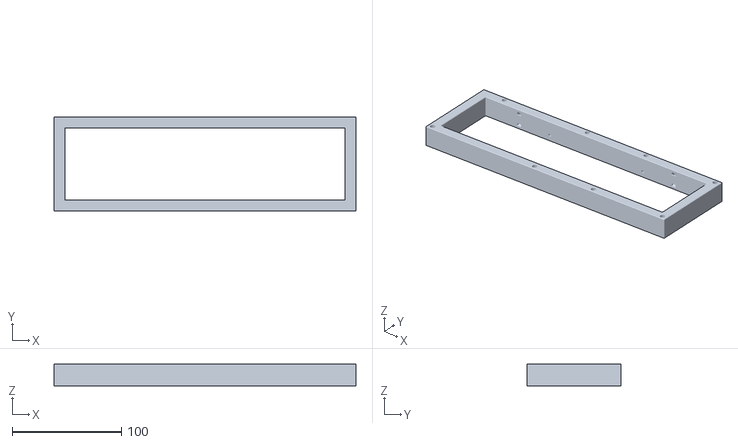
[picture p125: CAD file, 2023-02-27]
models/voron/ercf/mounts/ercf-french-cleat/stl/frame-9.stl
276.0 x 86.0 x 20.0
