geoffrey-young/3D-Printing/models/voron/ercf/random/gear-box-back-metal-80T.stl

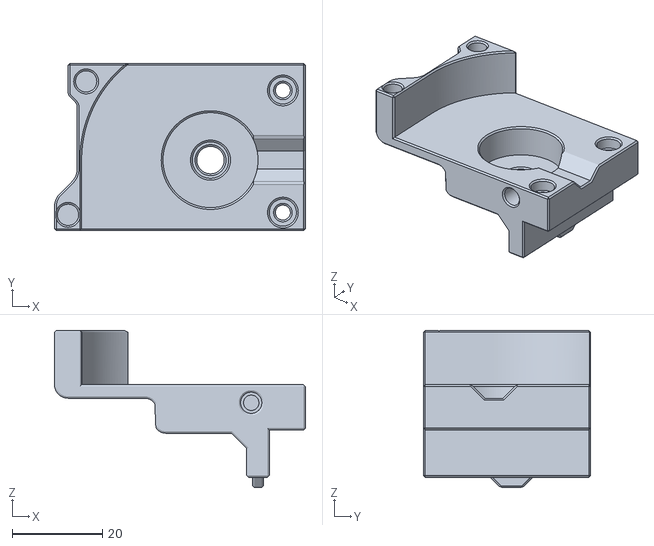
[picture p126: CAD file, 2023-01-15]
models/voron/ercf/random/gear-box-back-metal-80T.stl
55.5 x 37.0 x 34.8
