geoffrey-young/3D-Printing/models/creality/ender-3-v2/z-drive-helpers/stl/bottom-bracket.stl

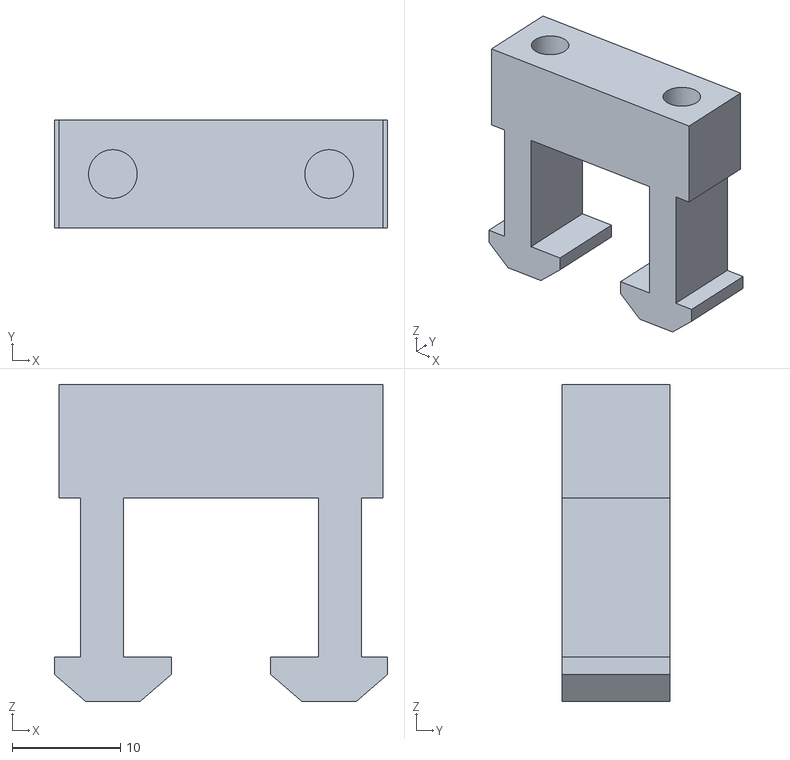
[picture p127: CAD file, 2021-06-09]
models/creality/ender-3-v2/z-drive-helpers/stl/bottom-bracket.stl
30.8 x 10.0 x 29.3
