geoffrey-young/3D-Printing/models/voron/2.4/stl/chains/xy_chain_end-inner.stl

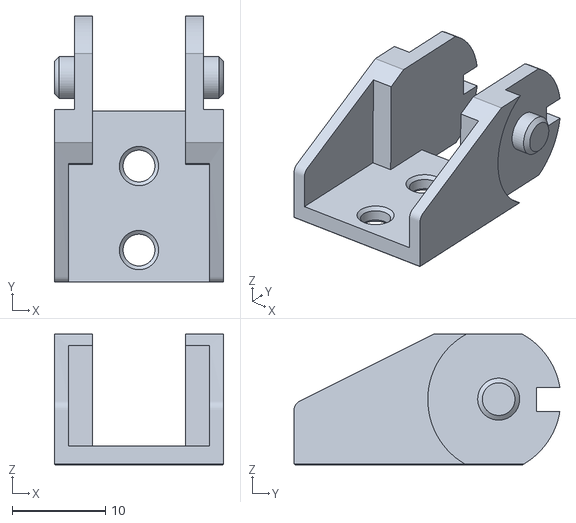
[picture p128: CAD file, 2021-07-02]
models/voron/2.4/stl/chains/xy_chain_end-inner.stl
18.1 x 28.5 x 14.0
