geoffrey-young/3D-Printing/models/voron/enderwire/stl/new/extruder-knob.stl

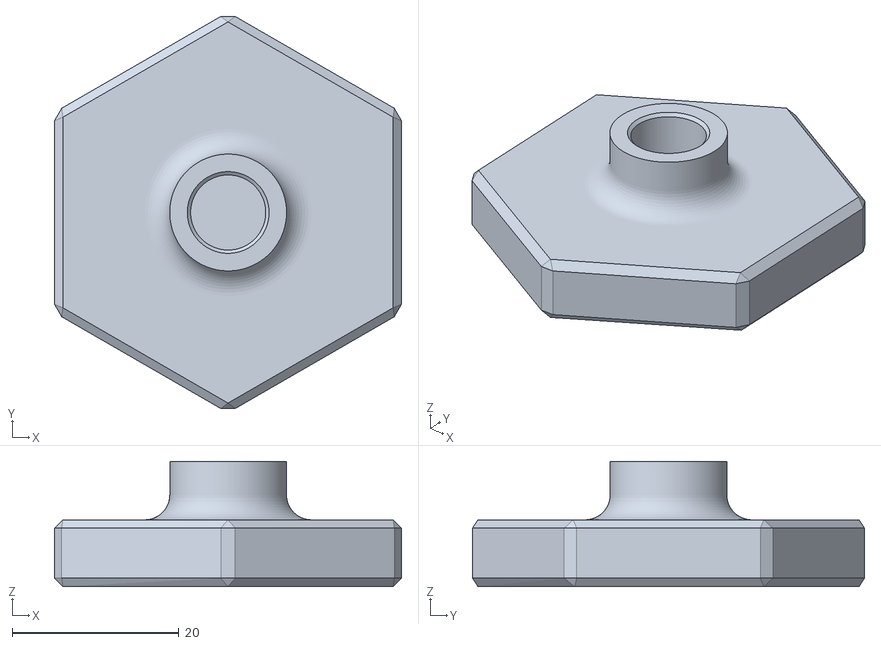
[picture p129: CAD file, 2022-06-13]
models/voron/enderwire/stl/new/extruder-knob.stl
41.6 x 47.0 x 15.0
