geoffrey-young/3D-Printing/models/voron/enderwire/stl/replacements/keybak_gantry_anchor.stl

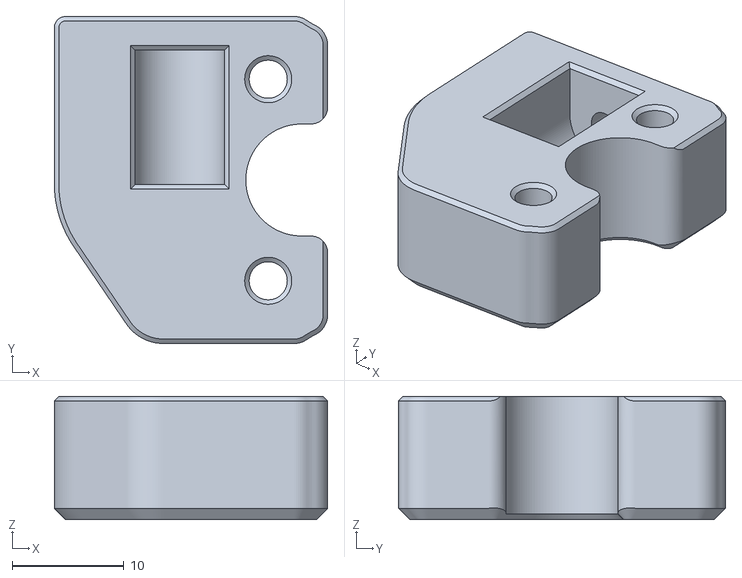
[picture p130: CAD file, 2022-06-13]
models/voron/enderwire/stl/replacements/keybak_gantry_anchor.stl
24.4 x 29.2 x 11.0
