geoffrey-young/3D-Printing/models/voron/ercf/mounts/bridge/stl/bridge-mount-6.stl

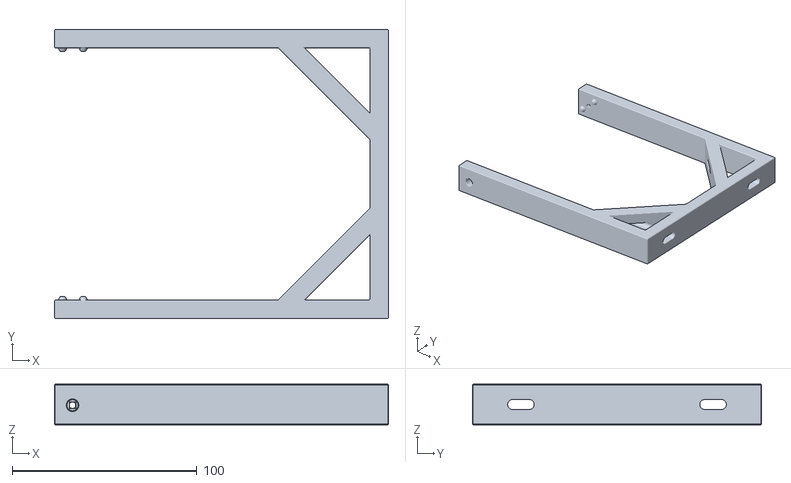
[picture p131: CAD file, 2023-04-11]
models/voron/ercf/mounts/bridge/stl/bridge-mount-6.stl
180.8 x 156.4 x 22.0
