geoffrey-young/3D-Printing/models/voron/ercf/mounts/ercf-french-cleat/stl/wall-mount-9.stl

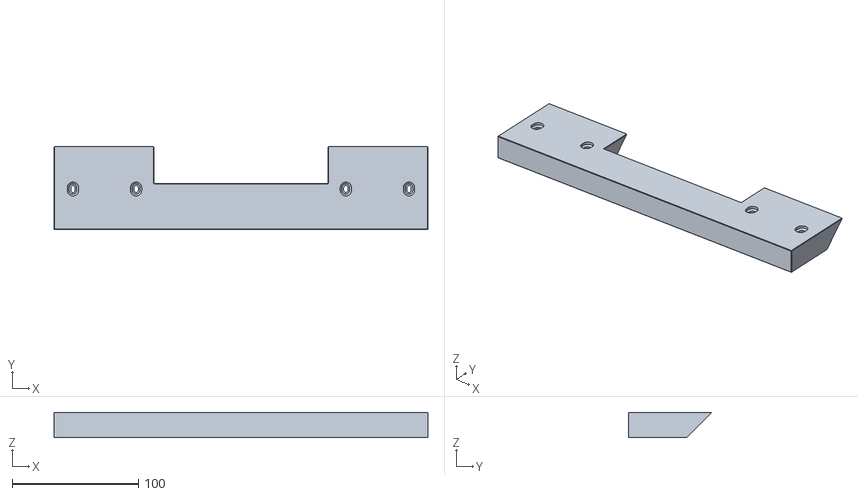
[picture p132: CAD file, 2022-11-07]
models/voron/ercf/mounts/ercf-french-cleat/stl/wall-mount-9.stl
296.0 x 65.7 x 20.0
