geoffrey-young/3D-Printing/models/voron/ercf/random/servo-arm-dfh.stl

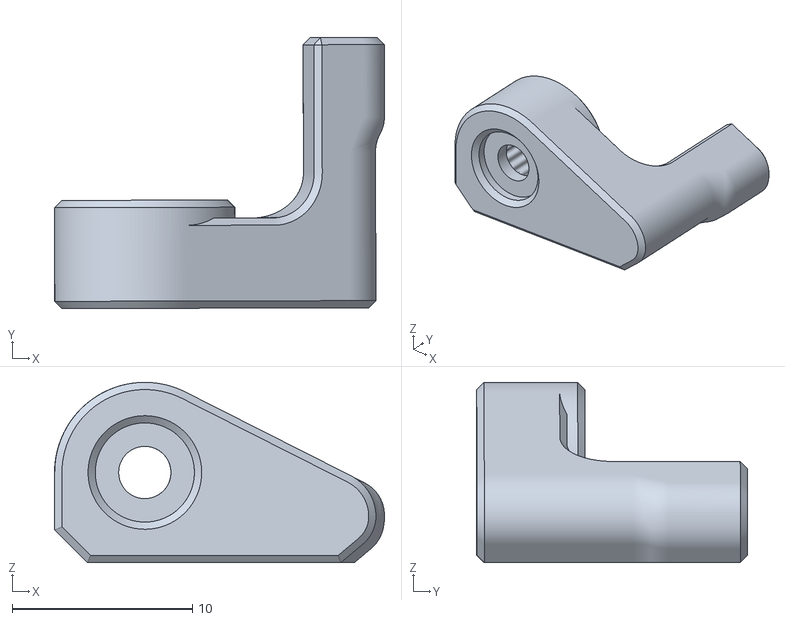
[picture p133: CAD file, 2023-01-12]
models/voron/ercf/random/servo-arm-dfh.stl
18.3 x 15.0 x 10.00
