geoffrey-young/3D-Printing/models/voron/enderwire/stl/new/extruder-mount.stl

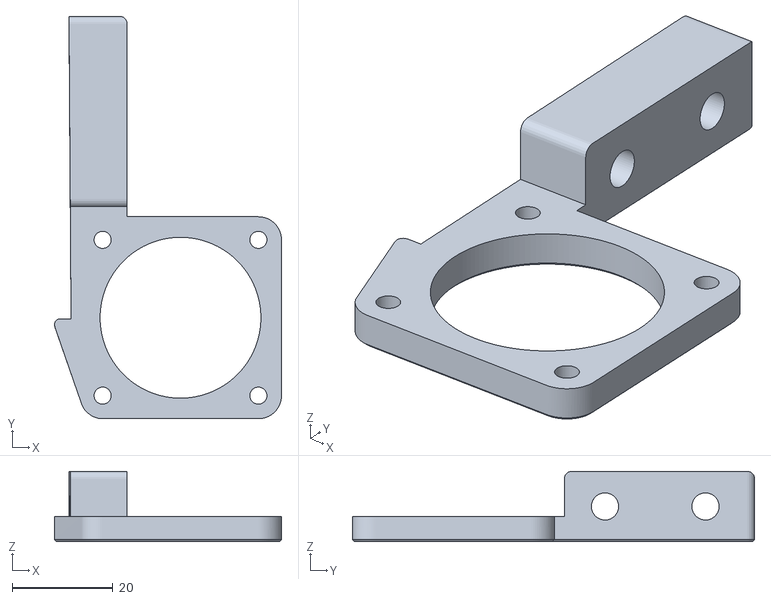
[picture p134: CAD file, 2022-06-13]
models/voron/enderwire/stl/new/extruder-mount.stl
45.2 x 80.1 x 14.0
