geoffrey-young/3D-Printing/models/voron/enderwire/stl/replacements/keybak_idler_bracket.stl

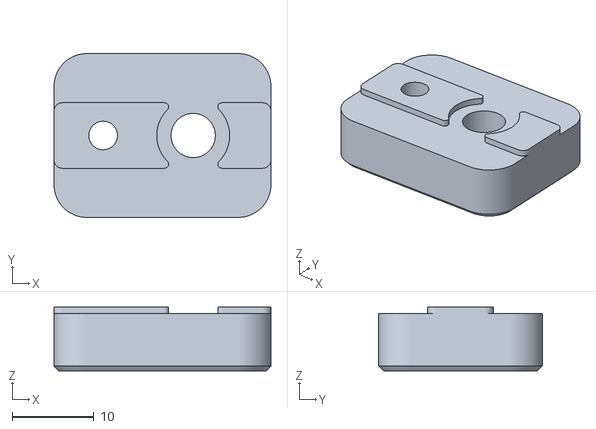
[picture p135: CAD file, 2022-06-13]
models/voron/enderwire/stl/replacements/keybak_idler_bracket.stl
26.5 x 20.0 x 7.80
