geoffrey-young/3D-Printing/models/voron/ercf/extender/stl/[a]_ecas-to-magnet-end_xN.stl

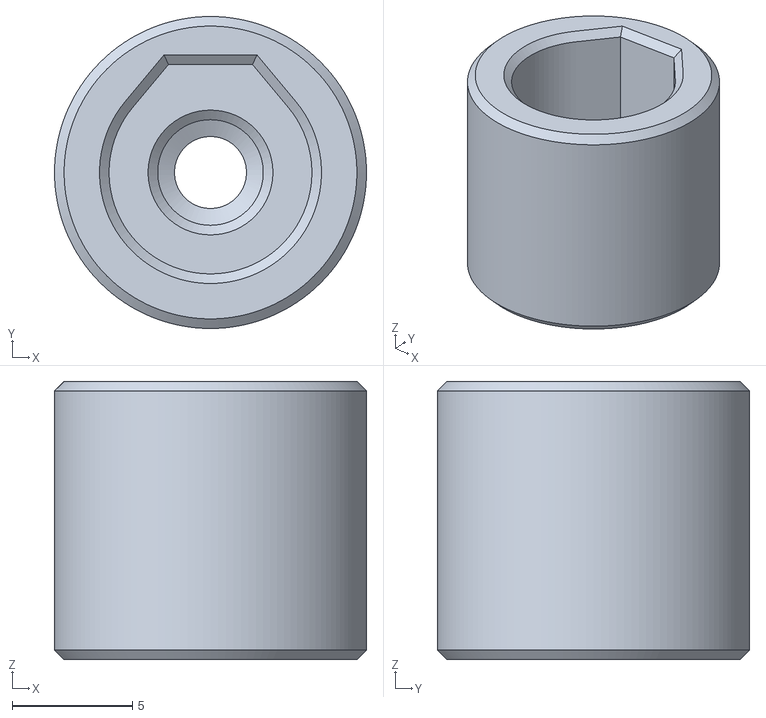
[picture p136: CAD file, 2023-04-11]
models/voron/ercf/extender/stl/[a]_ecas-to-magnet-end_xN.stl
13.0 x 13.0 x 11.6
