geoffrey-young/3D-Printing/models/voron/ercf/mounts/bridge/stl/bridge-ears.stl

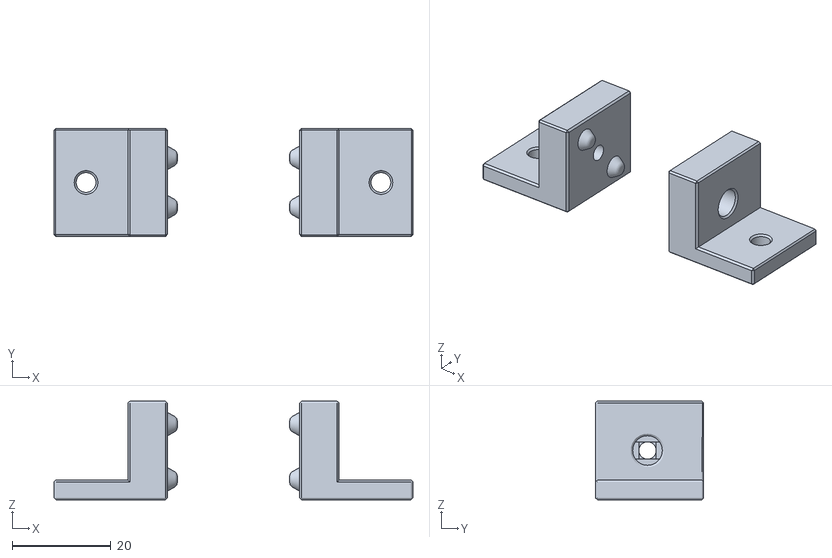
[picture p137: CAD file, 2023-03-25]
models/voron/ercf/mounts/bridge/stl/bridge-ears.stl
72.8 x 22.0 x 20.0
