geoffrey-young/3D-Printing/models/voron/ercf/mounts/ercf-french-cleat/stl/frame-cleat.stl

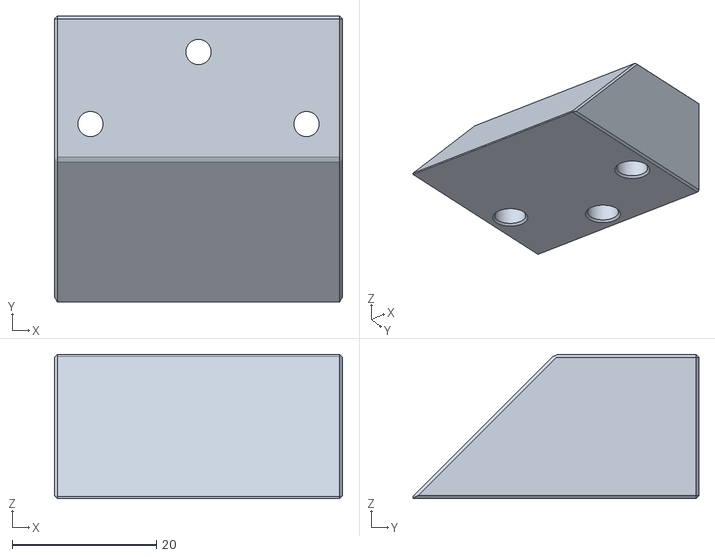
[picture p138: CAD file, 2022-11-07]
models/voron/ercf/mounts/ercf-french-cleat/stl/frame-cleat.stl
40.0 x 39.7 x 20.0
