geoffrey-young/3D-Printing/models/voron/ercf/random/encoder-right.stl

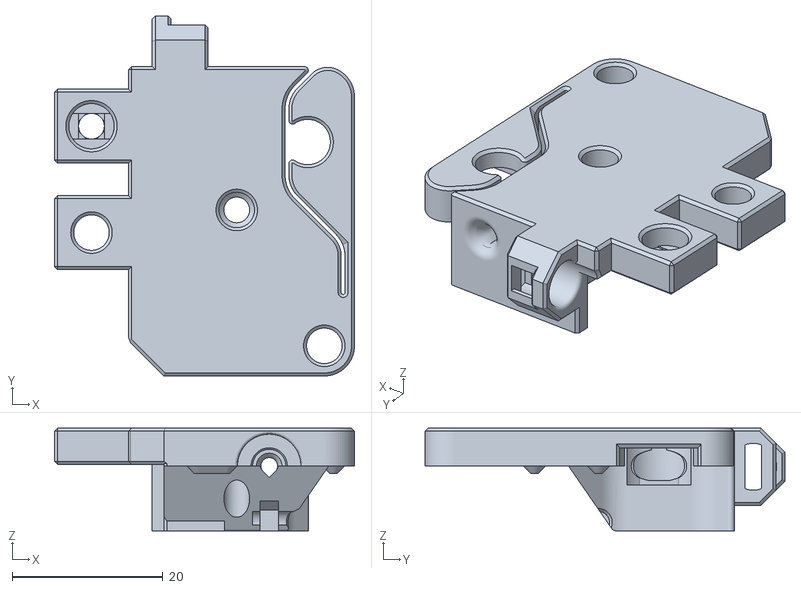
[picture p139: CAD file, 2023-01-06]
models/voron/ercf/random/encoder-right.stl
39.8 x 47.7 x 13.6
