geoffrey-young/3D-Printing/models/voron/enderwire/stl/new/wago-bed-mount.stl

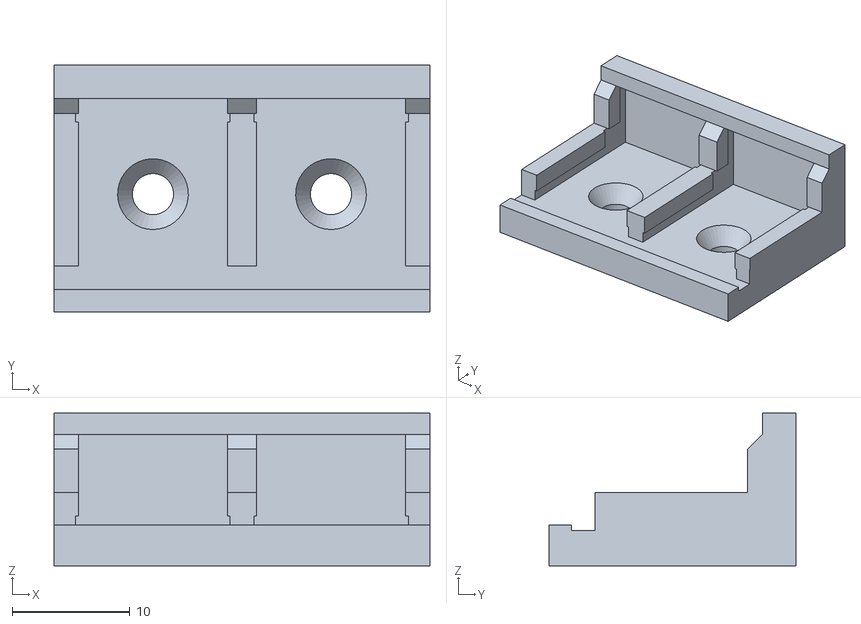
[picture p140: CAD file, 2022-06-13]
models/voron/enderwire/stl/new/wago-bed-mount.stl
32.0 x 21.0 x 13.0
