geoffrey-young/3D-Printing/models/voron/enderwire/stl/replacements/cover_4040_extrusion_cut_enderV2.stl

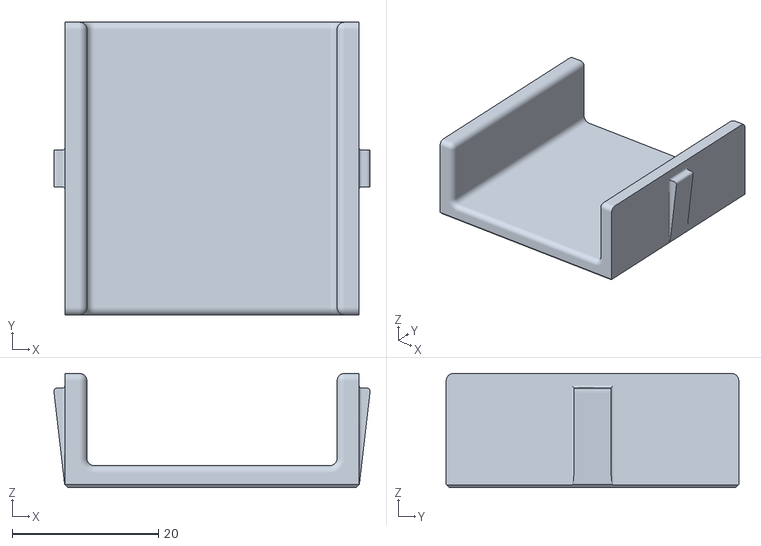
[picture p141: CAD file, 2022-06-13]
models/voron/enderwire/stl/replacements/cover_4040_extrusion_cut_enderV2.stl
43.2 x 40.0 x 15.6
