geoffrey-young/3D-Printing/models/voron/ercf/mounts/ercf-french-cleat/stl/wall-mount-end.stl

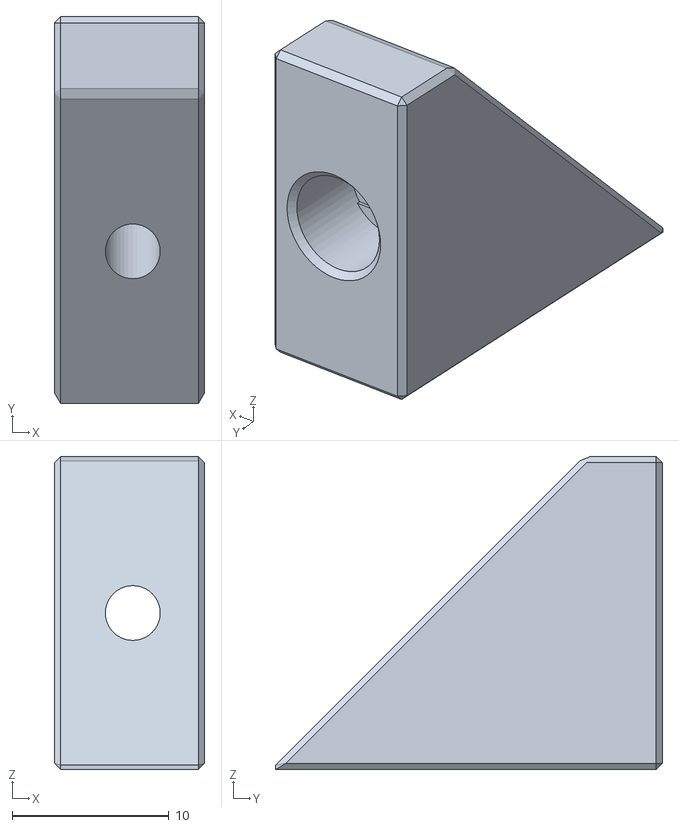
[picture p142: CAD file, 2022-11-07]
models/voron/ercf/mounts/ercf-french-cleat/stl/wall-mount-end.stl
9.60 x 24.7 x 20.0
