geoffrey-young/3D-Printing/models/voron/ercf/random/encoder-left.stl

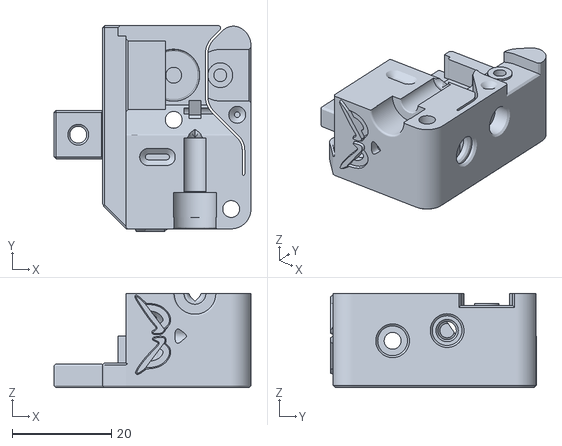
[picture p143: CAD file, 2023-01-06]
models/voron/ercf/random/encoder-left.stl
39.8 x 41.5 x 19.0
