geoffrey-young/3D-Printing/models/voron/enderwire/stl/new/m4-standoff-2mm.stl

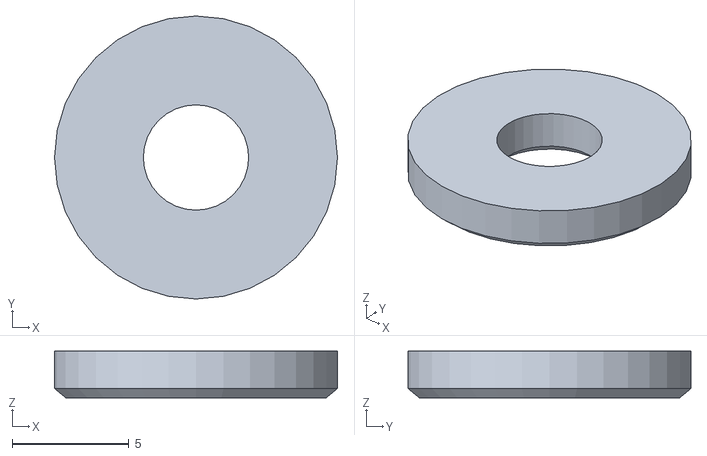
[picture p144: CAD file, 2022-06-13]
models/voron/enderwire/stl/new/m4-standoff-2mm.stl
12.1 x 12.1 x 2.00
