geoffrey-young/3D-Printing/models/voron/ercf/random/filament-block-n52.stl

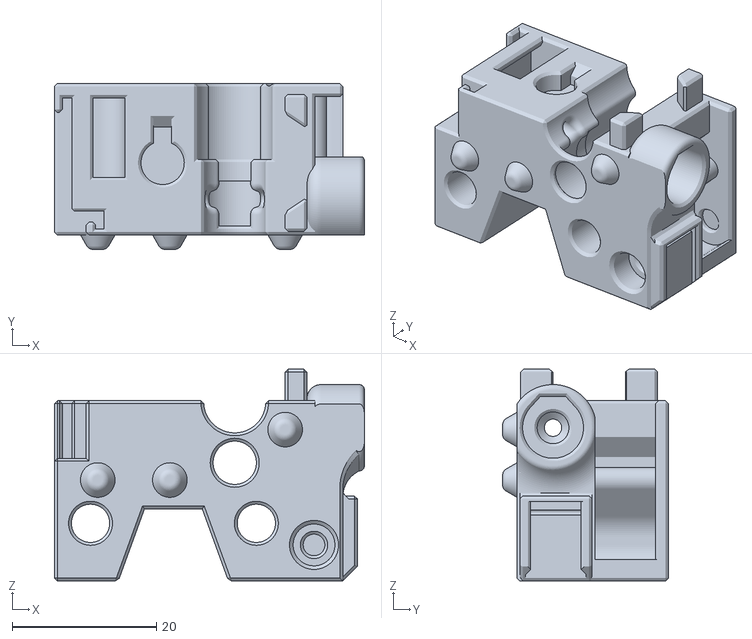
[picture p145: CAD file, 2023-01-06]
models/voron/ercf/random/filament-block-n52.stl
43.0 x 23.0 x 29.4
