geoffrey-young/3D-Printing/models/creality/ender-3-v2/z-drive-helpers/stl/z-axis-mount.stl

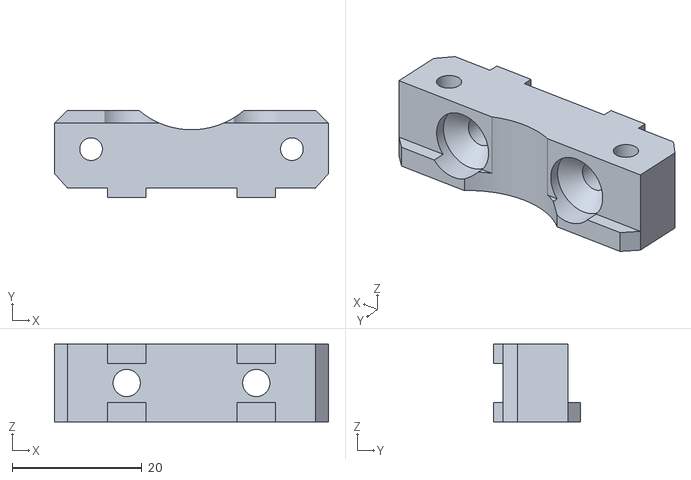
[picture p146: CAD file, 2021-06-09]
models/creality/ender-3-v2/z-drive-helpers/stl/z-axis-mount.stl
42.3 x 13.5 x 12.0
