geoffrey-young/3D-Printing/models/voron/enderwire/stl/new/y-endstop-bed-extension.stl

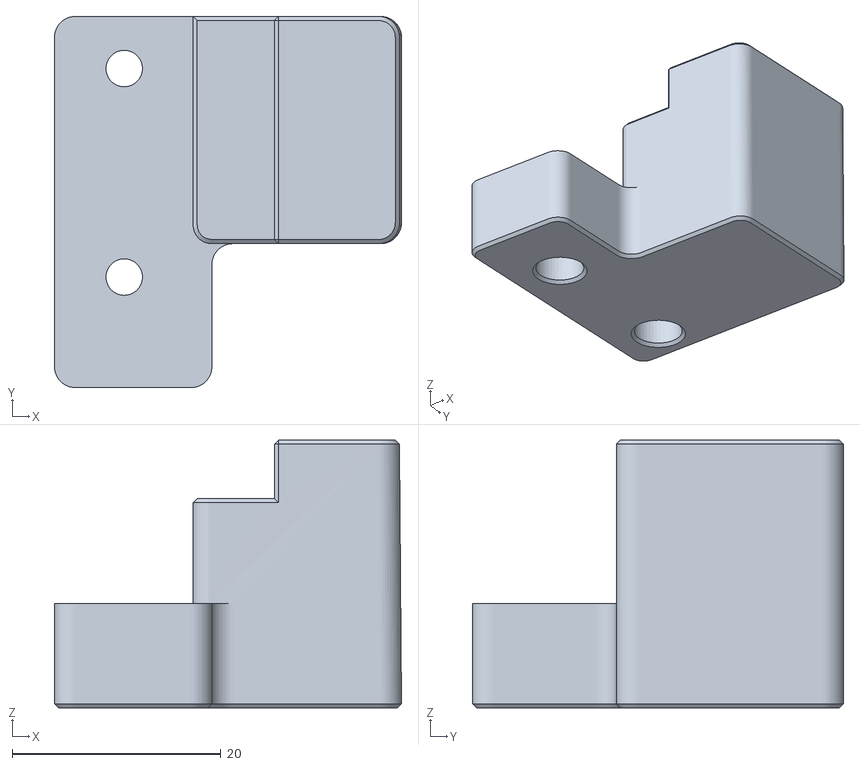
[picture p147: CAD file, 2022-06-13]
models/voron/enderwire/stl/new/y-endstop-bed-extension.stl
33.3 x 35.6 x 25.7
