geoffrey-young/3D-Printing/models/voron/ercf/random/encoder-sensor-mount.stl

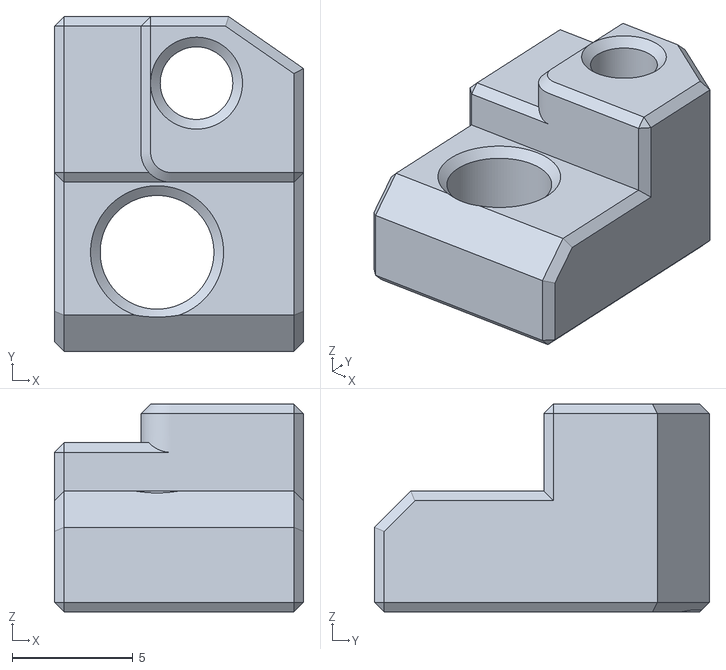
[picture p148: CAD file, 2023-01-06]
models/voron/ercf/random/encoder-sensor-mount.stl
10.3 x 13.9 x 8.60
