geoffrey-young/3D-Printing/models/creality/ender-3-v2/z-drive-helpers/stl/jig-guide.stl

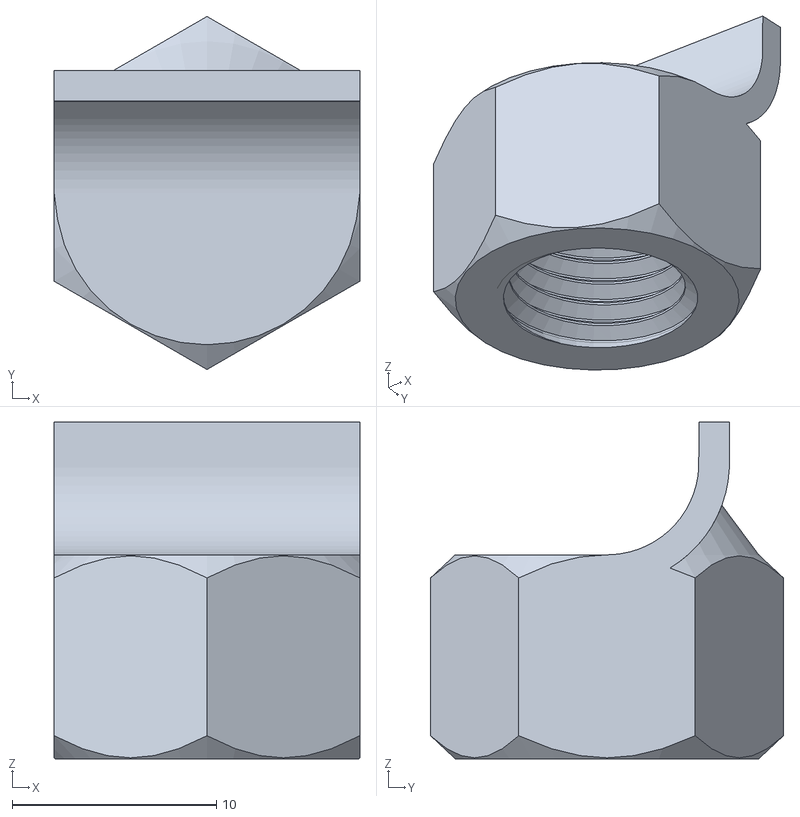
[picture p149: CAD file, 2021-06-09]
models/creality/ender-3-v2/z-drive-helpers/stl/jig-guide.stl
15.0 x 17.3 x 16.5
