geoffrey-young/3D-Printing/models/voron/enderwire/stl/new/brush-mount.stl

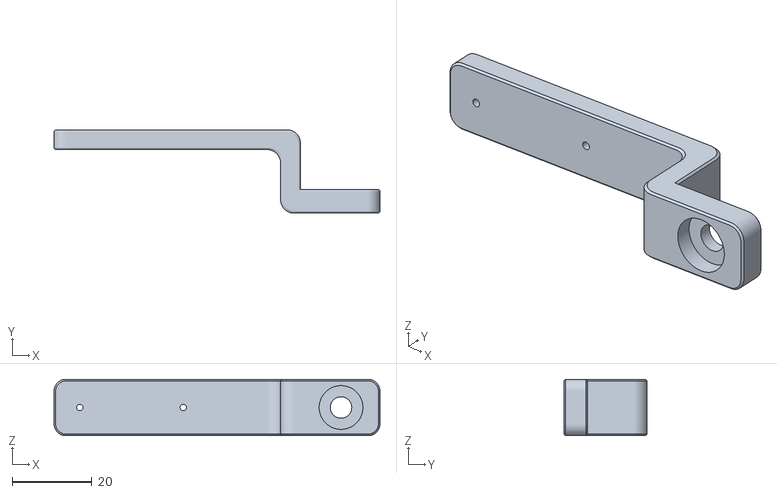
[picture p150: CAD file, 2022-06-13]
models/voron/enderwire/stl/new/brush-mount.stl
82.0 x 21.0 x 14.2
