geoffrey-young/3D-Printing/models/voron/enderwire/stl/new/2020-endcap.stl

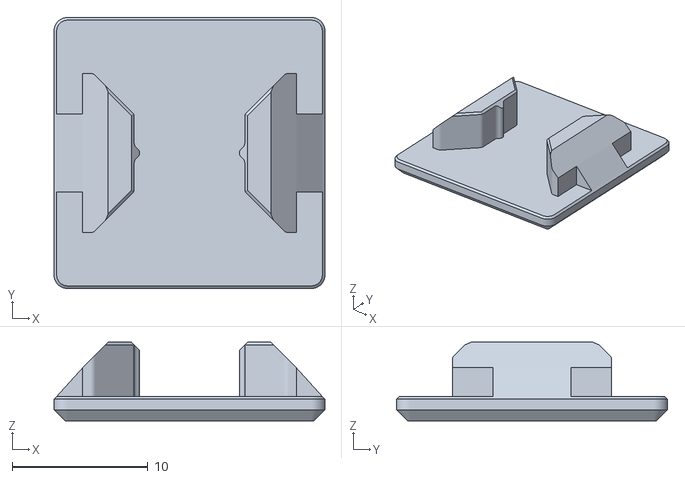
[picture p151: CAD file, 2022-06-13]
models/voron/enderwire/stl/new/2020-endcap.stl
20.0 x 20.0 x 5.80
