geoffrey-young/3D-Printing/models/voron/ercf/random/bar-clip-9.stl

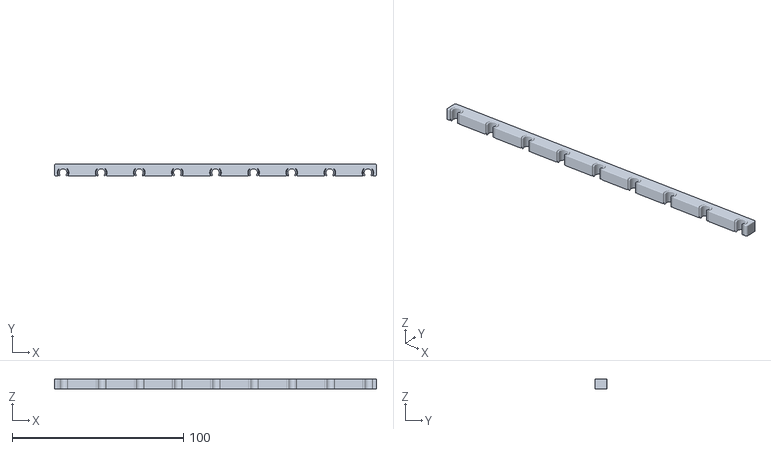
[picture p152: CAD file, 2022-12-31]
models/voron/ercf/random/bar-clip-9.stl
188.0 x 6.89 x 6.00
