geoffrey-young/3D-Printing/models/voron/enderwire/stl/new/y-bed-chain-extension-generic.stl

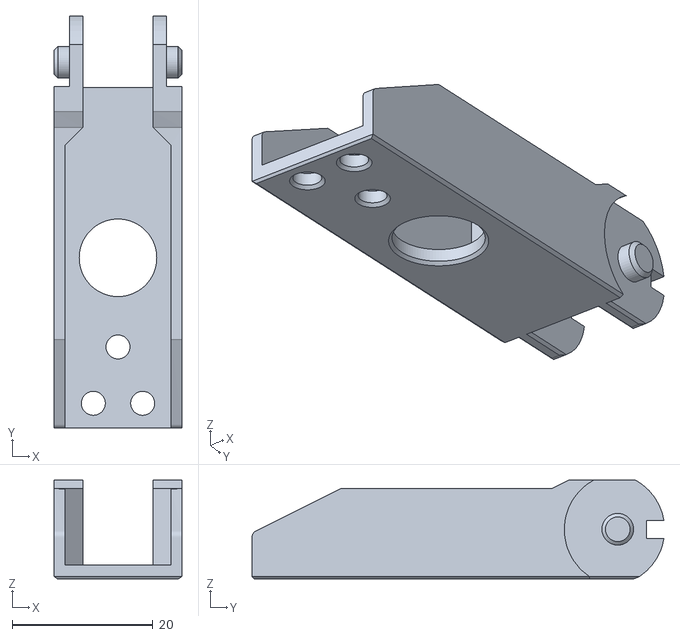
[picture p153: CAD file, 2022-06-13]
models/voron/enderwire/stl/new/y-bed-chain-extension-generic.stl
18.1 x 58.5 x 14.0
