geoffrey-young/3D-Printing/models/voron/ercf/random/mm-connector-cover-magnet.stl

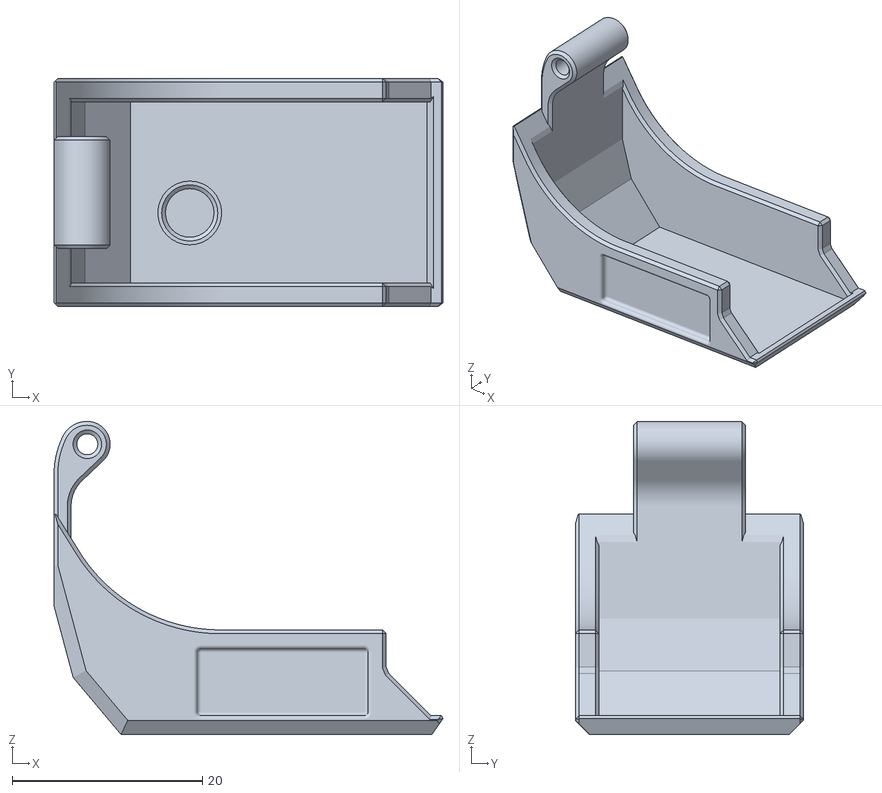
[picture p154: CAD file, 2022-12-13]
models/voron/ercf/random/mm-connector-cover-magnet.stl
40.9 x 24.0 x 32.9
