geoffrey-young/3D-Printing/models/voron/enderwire/stl/new/y-axis-350mm-extension.stl

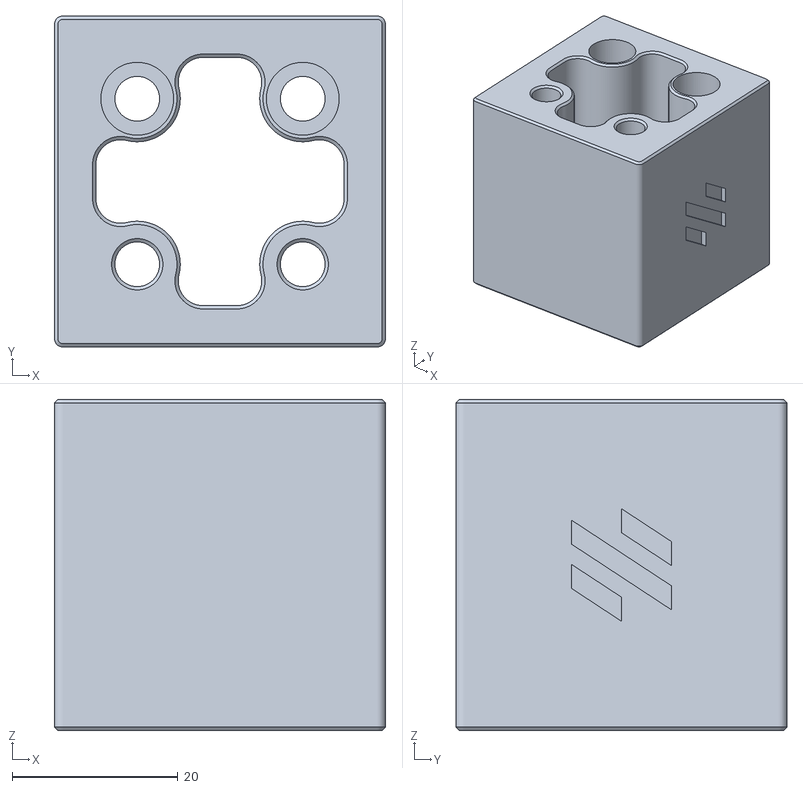
[picture p155: CAD file, 2022-06-13]
models/voron/enderwire/stl/new/y-axis-350mm-extension.stl
40.0 x 40.0 x 40.0
