geoffrey-young/3D-Printing/models/voron/enderwire/stl/new/amplifier-foot-mount.stl

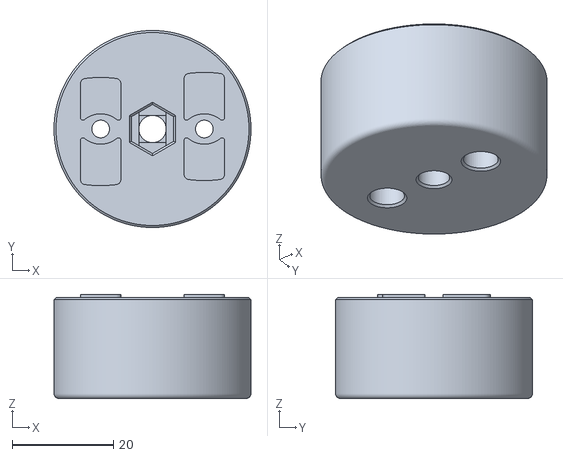
[picture p156: CAD file, 2022-06-13]
models/voron/enderwire/stl/new/amplifier-foot-mount.stl
39.0 x 39.0 x 20.6
