geoffrey-young/3D-Printing/models/voron/enderwire/stl/new/stealthbowden-plate.stl

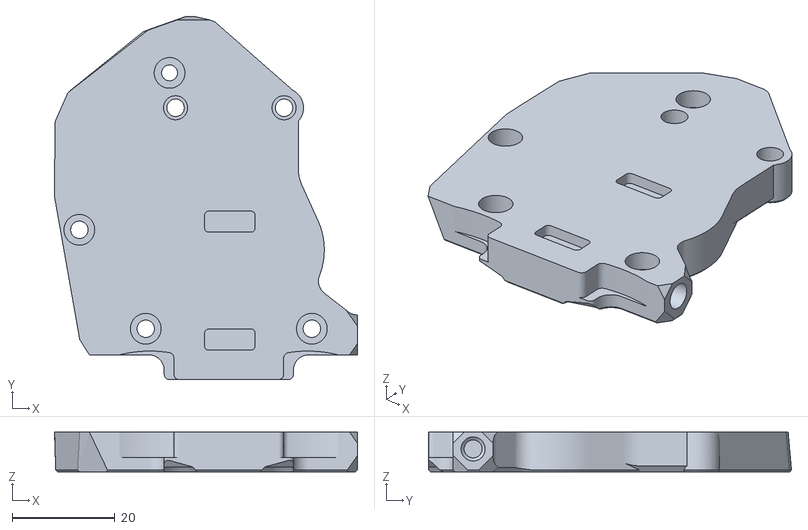
[picture p157: CAD file, 2022-06-13]
models/voron/enderwire/stl/new/stealthbowden-plate.stl
59.1 x 70.8 x 7.80
