geoffrey-young/3D-Printing/klipper/voron/v2/ercf-hh/ercf_software.cfg

########################################################################
# Simplified subset of commands For visability in Mainsail/Fluidd UI
########################################################################
[gcode_macro ERCF__EJECT]
gcode: ERCF_EJECT

[gcode_macro ERCF__UNLOCK]
gcode: ERCF_UNLOCK

[gcode_macro ERCF__HOME]
gcode:
    {% set TOOL = params.TOOL|default(-1)|int %}
    {% set FORCE_UNLOAD = params.TOOL|default(-1)|int %}
    ERCF_HOME TOOL={TOOL} FORCE_UNLOAD={FORCE_UNLOAD}



# I don't use any of the defaults as set in this macro
# see hotends/rapido.cfg and hotends/dragon-sf.cfg for my settings

########################################################################
# Standalone Tip Forming (for rapid tuning of Slicer values)
########################################################################
[gcode_macro _ERCF_FORM_TIP_STANDALONE]
description: Standalone macro that mimics SS process

# Unloading and Ramming values - Initial moves to form and shape tip
variable_unloading_speed_start: 80     # Fast here to seperate the filament from meltzone (Very intitial retract SS uses distance of E-15)
variable_unloading_speed: 20           # Too fast forms excessively long tip or hair. Slow is better here UNLOADING_SPEED_START/COOLING_MOVES seems a good start
variable_ramming_volume: 20            # in mm3 SS default values = 2, 5, 9, 13, 18, 23, 27. Only Used to Simulate SS Ramming during standalone
variable_ss_ramming: 0                 # Set to 0 when using standalone ramming (RAMMING_VOLUME) or tuning, 1 to let the slicer do it

# Cooling Move Values - To cool the tip formed and separate from strings
variable_cooling_tube_position: 35     # Dragon ST: 35, Dragon HF: 30, Mosquito: 3, Revo: 35, Phaetus Rapido HF: 43;  Measured from Top of Heater Block to Top of Heatsink
variable_cooling_tube_length: 10       # Dragon ST: 15, Dragon HF: 10, Mosquito: 20, Revo: 10, Phaetus Rapido HF: 22; Measured from Nozzle to Top of Heater Block
variable_initial_cooling_speed: 10     # Slow to solidify tip and cool string if formed.
variable_final_cooling_speed: 50       # High speed break the string formed. Too fast = tip deformation during eject. Too Slow = long string/no seperation
variable_toolchange_temp: 0            # Used if you want to lower temp during toolchanges default 0
variable_cooling_moves: 4              # 2-4 is a good start

# SkinnyDip values - To burn off VERY FINE hairs only (This is NOT for long tip reshaping)
variable_use_skinnydip: 1              # Tune this LAST, this is for removal of VERY FINE hairs only (Different than a long tip)
variable_skinnydip_distance: 30        # Start just under Cooling_tube_position and increase - Will depend on how much Ramming Volume is used
variable_dip_insertion_speed: 30       # Medium-Slow - Just long enough to melt the fine hairs. Too slow will pull up molten filament
variable_dip_extraction_speed: 70      # Around 2x Insertion speed, Prevents forming new hairs
variable_melt_zone_pause: 0            # in milliseconds - default 0
variable_cooling_zone_pause: 0         # in milliseconds - default 0 - If you need to adjust here its possible Dip Insertion too slow
variable_use_fast_skinnydip: 0         # Skip the toolhead temp change during skinnydip move - default 0

# Park filament ready to eject
# variable_parking_distance: 0          # TODO: SS parks filament after final cooling move

# Final Eject - for standalone tuning only
variable_final_eject: 0                # default 0, enable during standalone tuning process to eject the filament

gcode:
# Initialize Paramaters
    {% set UNLOADING_SPEED_START = params.UNLOADING_SPEED_START|default(printer['gcode_macro _ERCF_FORM_TIP_STANDALONE']['unloading_speed_start']) %}
    {% set UNLOADING_SPEED = params.UNLOADING_SPEED|default(printer['gcode_macro _ERCF_FORM_TIP_STANDALONE']['unloading_speed']) %}
    {% set RAMMING_VOLUME = params.RAMMING_VOLUME|default(printer['gcode_macro _ERCF_FORM_TIP_STANDALONE']['ramming_volume'], True) %}
    {% set SS_RAMMING = params.SS_RAMMING|default(printer['gcode_macro _ERCF_FORM_TIP_STANDALONE']['ss_ramming'], True) %}
    {% set COOLING_TUBE_LENGTH = params.COOLING_TUBE_LENGTH|default(printer['gcode_macro _ERCF_FORM_TIP_STANDALONE']['cooling_tube_length']) %}
    {% set COOLING_TUBE_POSITION = params.COOLING_TUBE_POSITION|default(printer['gcode_macro _ERCF_FORM_TIP_STANDALONE']['cooling_tube_position']) %}
    {% set INITIAL_COOLING_SPEED = params.INITIAL_COOLING_SPEED|default(printer['gcode_macro _ERCF_FORM_TIP_STANDALONE']['initial_cooling_speed']) %}
    {% set FINAL_COOLING_SPEED = params.FINAL_COOLING_SPEED|default(printer['gcode_macro _ERCF_FORM_TIP_STANDALONE']['final_cooling_speed']) %}
    {% set COOLING_MOVES = params.COOLING_MOVES|default(printer['gcode_macro _ERCF_FORM_TIP_STANDALONE']['cooling_moves']) %}
    {% set TOOLCHANGE_TEMP = params.TOOLCHANGE_TEMP|default(printer['gcode_macro _ERCF_FORM_TIP_STANDALONE']['toolchange_temp'],True) %}
    {% set USE_SKINNYDIP = params.USE_SKINNYDIP|default(printer['gcode_macro _ERCF_FORM_TIP_STANDALONE']['use_skinnydip'], True) %}
    {% set USE_FAST_SKINNYDIP = params.USE_FAST_SKINNYDIP|default(printer['gcode_macro _ERCF_FORM_TIP_STANDALONE']['use_fast_skinnydip'], True) %}
    {% set SKINNYDIP_DISTANCE = params.SKINNYDIP_DISTANCE|default(printer['gcode_macro _ERCF_FORM_TIP_STANDALONE']['skinnydip_distance']) %}
    {% set DIP_INSERTION_SPEED = params.DIP_INSERTION_SPEED|default(printer['gcode_macro _ERCF_FORM_TIP_STANDALONE']['dip_insertion_speed']) %}
    {% set DIP_EXTRACTION_SPEED = params.DIP_EXTRACTION_SPEED|default(printer['gcode_macro _ERCF_FORM_TIP_STANDALONE']['dip_extraction_speed']) %}
    {% set MELT_ZONE_PAUSE = params.MELT_ZONE_PAUSE|default(printer['gcode_macro _ERCF_FORM_TIP_STANDALONE']['melt_zone_pause']) %}
    {% set COOLING_ZONE_PAUSE = params.COOLING_ZONE_PAUSE|default(printer['gcode_macro _ERCF_FORM_TIP_STANDALONE']['cooling_zone_pause']) %}
    {% set FINAL_EJECT = params.FINAL_EJECT|default(printer['gcode_macro _ERCF_FORM_TIP_STANDALONE']['final_eject'], True) %}

    G91
    G92 E0

    #---------------------------------#
    #-Tip forming Process begins here-#
    #---------------------------------#

    SET_PRESSURE_ADVANCE ADVANCE=0
    {% set OLD_TEMP = printer.extruder.target %}
    {% if SS_RAMMING|int == 0 %} # Standalone Ramming
        {% set RATIO = (RAMMING_VOLUME|float) /23.0 %}
        G1 E{0.5784 * RATIO|float} F299 #7
        G1 E{0.5834 * RATIO|float} F302 #3
        G1 E{0.5918 * RATIO|float} F306 #6
        G1 E{0.6169 * RATIO|float} F319 #6
        G1 E{0.3393 * RATIO|float} F350 #0
        G1 E{0.3363 * RATIO|float} F350 #0
        G1 E{0.7577 * RATIO|float} F392 #6
        G1 E{0.8382 * RATIO|float} F434 #3
        G1 E{0.7776 * RATIO|float} F469 #9
        G1 E{0.1293 * RATIO|float} F469 #9
        G1 E{0.9673 * RATIO|float} F501 #2
        G1 E{1.0176 * RATIO|float} F527 #2
        G1 E{0.5956 * RATIO|float} F544 #6
        G1 E{0.4555 * RATIO|float} F544 #6
        G1 E{1.0662 * RATIO|float} F552 #4
    {% endif %}

    # Set toolchange temperature just prior to filament being extracted from melt zone and wait for set point
    # (SKINNYDIP -- normal mode only)
    # Only used if changing between filament types eg. ABS-->PLA
    {% if TOOLCHANGE_TEMP|float > 0 and USE_FAST_SKINNYDIP|int == 0 %}
         M109 S{TOOLCHANGE_TEMP}
    {% endif %}

    # Unloading - This is where the tip spear shape comes from Faster=longer/pointer/higher stringing
    {% set TOTAL_RETRACTION_DISTANCE = COOLING_TUBE_POSITION|float + COOLING_TUBE_LENGTH|float / 2 - 15 %}
    G1 E-15 F{1.0 * UNLOADING_SPEED_START|float * 60} # Default value from SS - Cannot modify
    G1 E-{0.7 * TOTAL_RETRACTION_DISTANCE} F{1.0 * UNLOADING_SPEED|float * 60}
    G1 E-{0.2 * TOTAL_RETRACTION_DISTANCE} F{0.5 * UNLOADING_SPEED|float * 60}
    G1 E-{0.1 * TOTAL_RETRACTION_DISTANCE} F{0.3 * UNLOADING_SPEED|float * 60}

    {% if TOOLCHANGE_TEMP|float > 0 and USE_FAST_SKINNYDIP|int == 1 %}
        M104 S{TOOLCHANGE_TEMP}
    {% endif %}

    # Generate Cooling Moves - Solidifies tip shape and helps break strings if formed
    {% set SPEED_INC = (FINAL_COOLING_SPEED|float - INITIAL_COOLING_SPEED|float) / (2 * COOLING_MOVES|float - 1) %}
    {% for move in range(COOLING_MOVES|int) %}
        G1 E{COOLING_TUBE_LENGTH} F{(INITIAL_COOLING_SPEED|float + SPEED_INC*move*2) * 60}
        G1 E-{COOLING_TUBE_LENGTH} F{(INITIAL_COOLING_SPEED|float + SPEED_INC*(move*2+1)) * 60}
    {% endfor %}

    # Wait for extruder to reach toolchange temperature after cooling moves complete (SKINNYDIP--fast mode only)
    {% if TOOLCHANGE_TEMP|float > 0 and USE_FAST_SKINNYDIP|int == 1 %}
        M109 S{TOOLCHANGE_TEMP}
    {% endif %}

    # Skinny dip Move - burns off VERY FINE hairs
    {% if USE_SKINNYDIP|int == 1 %}
        G1 E{SKINNYDIP_DISTANCE} F{DIP_INSERTION_SPEED|float * 60}
        G4 P{MELT_ZONE_PAUSE}
        G1 E-{SKINNYDIP_DISTANCE} F{DIP_EXTRACTION_SPEED|float * 60}
        G4 P{COOLING_ZONE_PAUSE}
    {% endif %}

    {% if TOOLCHANGE_TEMP|float > 0 %}
        M104 S{OLD_TEMP}
    {% endif %}

    # Park filament
    # TODO: park filament after cooling/skinny dip. Maths to determine distance of previous moves to final parking distance

    # Eject once all shaping is done - Standalone mode only
    {% if FINAL_EJECT|int == 1 %}
        G92 E0
        G1 E-80 F3000
    {% endif %}

    G92 E0
    G90

###########################################################################
# EndlessSpool handling
# Note that EndlessSpool is an unsupervised filament change
###########################################################################
[gcode_macro _ERCF_ENDLESS_SPOOL_PRE_UNLOAD]
description: Pre unload routine for EndlessSpool changes
gcode:
    # This occurs prior to ERCF forming tip and ejecting the remains of the old filament
    #
    # Typically you would move toolhead to your park position so oozing is not a problem
    #
    # This is probably similar to what you do in your PAUSE macro and you could simply call that here...
    # (this call works with reference PAUSE macro supplied in client_macros.cfg)

    PAUSE

[gcode_macro _ERCF_ENDLESS_SPOOL_POST_LOAD]
description: Optional post load routine for EndlessSpool changes
gcode:
    # This occurs after ERCF has loaded the new filament from the next spool in rotation
    # ERCF will have loaded the new filament to the nozzle the same way as a normal filament
    # swap. Previously configured Pressure Advance will be retained.
    # 
    # This would be a place to purge additional filament if necessary (it really shouldn't be)
    # and clean nozzle if your printer is suitably equipped.
    #
    # This is probably similar to what you do in your RESUME macro and you could simply call that here...
    # (this call works with reference RESUME macro supplied in client_macros.cfg)

    RESUME
