geoffrey-young/3D-Printing/klipper/voron/v2/axes.cfg

# required for independent movement of rear z motors to level the back when it sags
# see RAISE_BACK in macros.cfg
[force_move]
enable_force_move: True


# B motor
[stepper_x]
step_pin: PE11
dir_pin: PE10
enable_pin: !PE9
rotation_distance: 40
microsteps: 32
full_steps_per_rotation:200

endstop_pin: ^PB14
position_min: 0
position_endstop: 346
position_max: 346

homing_speed: 75
homing_retract_dist: 5

[tmc2209 stepper_x]
uart_pin: PE7
sense_resistor: 0.150 #tmc2226
interpolate: False
stealthchop_threshold: 0
run_current: 0.80

#driver_TBL: 2
#driver_TOFF: 2
#driver_HEND: 1
#driver_HSTRT: 4
#driver_PWM_LIM: 8 
#driver_PWM_GRAD: 8
#driver_PWM_FREQ: 1
#driver_PWM_REG: 4


# A motor
[stepper_y]
step_pin: PD8
dir_pin: PB12
enable_pin: !PD9
rotation_distance: 40
microsteps: 32
full_steps_per_rotation:200

endstop_pin: ^PB13
position_min: 0
position_endstop: 350
position_max: 350

homing_speed: 75
homing_retract_dist: 5

[tmc2209 stepper_y]
uart_pin: PE15
sense_resistor: 0.150 #tmc2226
interpolate: False
stealthchop_threshold: 0
run_current: 0.80

#driver_TBL: 2
#driver_TOFF: 2
#driver_HEND: 1
#driver_HSTRT: 4
#driver_PWM_LIM: 8 
#driver_PWM_GRAD: 8
#driver_PWM_FREQ: 1
#driver_PWM_REG: 4


[stepper_z]
step_pin: PD14
dir_pin: !PD13
enable_pin: !PD15
rotation_distance: 40
gear_ratio: 80:16
microsteps: 32

endstop_pin: ^PA0

position_max: 320
position_min: -1.5
homing_speed: 8
second_homing_speed: 3
homing_retract_dist: 3

[tmc2209 stepper_z]
uart_pin: PD10
uart_address: 0
interpolate: False
stealthchop_threshold: 0
run_current: 0.80

[stepper_z1]
step_pin: PE6
dir_pin: PC13
enable_pin: !PE5
rotation_distance: 40
gear_ratio: 80:16
microsteps: 32

[tmc2209 stepper_z1]
uart_pin: PC14
interpolate: False
stealthchop_threshold: 0
run_current: 0.80

[stepper_z2]
step_pin: PE2
dir_pin: !PE4
enable_pin: !PE3
rotation_distance: 40
gear_ratio: 80:16
microsteps: 32

[tmc2209 stepper_z2]
uart_pin: PC15
interpolate: False
stealthchop_threshold: 0
run_current: 0.80

[stepper_z3]
step_pin: PD12
dir_pin: PC4
enable_pin: !PE8
rotation_distance: 40
gear_ratio: 80:16
microsteps: 32

[tmc2209 stepper_z3]
uart_pin: PA15
interpolate: False
stealthchop_threshold: 0
run_current: 0.80
