geoffrey-young/3D-Printing/klipper/voron/macros/filament.cfg

[gcode_macro FILAMENT_RUNOUT]
description: filament runout event
gcode:

  {% set msg = "filament runout triggered" %}
  RESPOND MSG="{msg}" TYPE=error
  NOTIFY MSG="{msg}"
  DISABLE_FILAMENT_SENSOR
  PAUSE


[gcode_macro ENABLE_FILAMENT_SENSOR]
description: enable filament runout sensor
variable_skip: False
gcode:
  {% if skip %}
    M118 skipping ENABLE_FILAMENT_SENSOR
  {% else %}
    M118 enabling filament runout sensor...
    SET_FILAMENT_SENSOR SENSOR=filament ENABLE=1
  {% endif %}

  FILAMENT_SENSOR_STATUS


[gcode_macro DISABLE_FILAMENT_SENSOR]
description: disable filament runout sensor
gcode:
  SET_FILAMENT_SENSOR SENSOR=filament ENABLE=0
  FILAMENT_SENSOR_STATUS


[gcode_macro RUNOUT_SENSOR_STATUS]
description: filament runout sensor status
gcode:
  {% set sensor = (printer['filament_switch_sensor filament'] or printer['filament_motion_sensor filament']) %}
  {% if sensor %}
    {% set enabled = "<span class=success--text>true</span>" if sensor.enabled else "<span class=error--text>false</span>" %}
    {% set detected = "<span class=success--text>true</span>" if sensor.filament_detected else "<span class=error--text>false</span>" %}
    M118 { "filament runout sensor enabled: %s, filament: %s" % (enabled, detected) }
  {% else %}
    M118 no filament runout sensor found
  {% endif %}


[gcode_macro ENABLE_TOOLHEAD_SENSOR]
description: enable toolhead filament sensor
gcode:
  M118 enabling toolhead filament sensor...
  SET_FILAMENT_SENSOR SENSOR=toolhead_sensor ENABLE=1

  TOOLHEAD_SENSOR_STATUS


[gcode_macro DISABLE_TOOLHEAD_SENSOR]
description: disable filament runout sensor
gcode:
  SET_FILAMENT_SENSOR SENSOR=toolhead_sensor ENABLE=0
  TOOLHEAD_SENSOR_STATUS


[gcode_macro TOOLHEAD_SENSOR_STATUS]
description: ercf sensor status
gcode:
  {% set sensor = printer['filament_switch_sensor toolhead_sensor'] %}
  {% if sensor %}
    {% set enabled = "<span class=success--text>true</span>" if sensor.enabled else "<span class=error--text>false</span>" %}
    {% set detected = "<span class=success--text>true</span>" if sensor.filament_detected else "<span class=error--text>false</span>" %}
    M118 { "toolhead sensor enabled: %s, filament: %s" % (enabled, detected) }
  {% else %}
    M118 toolhead sensor not found?
  {% endif %}


[gcode_macro FILAMENT_SENSOR_STATUS]
description: filament runout sensor status
gcode:
  RUNOUT_SENSOR_STATUS
  TOOLHEAD_SENSOR_STATUS


[gcode_macro SKIP_FILAMENT_SENSOR]
description: skip filament sensor enables for the duration of the print
gcode:
  {% set skip = params.SKIP|default(True, True)|int %}

  SET_GCODE_VARIABLE MACRO=ENABLE_FILAMENT_SENSOR VARIABLE=skip VALUE={skip}

  M118 { 'SKIP_FILAMENT_SENSOR = %d' % (skip) }


[gcode_macro FILAMENT_LOAD]
description: slow load 75mm of filament
gcode:

  {% set first = 600 if printer.extruder.target >= 235 else 300 %}
  {% set second = 300 if printer.extruder.target >= 235 else 150 %}

  {% if printer.extruder.can_extrude %}
    SAVE_GCODE_STATE NAME=__filament__load
    NOTE_PRESSURE_ADVANCE
    SET_PRESSURE_ADVANCE ADVANCE=0
    M83
    G1 E25 F{first}
    G1 E25 F{second}
    G1 E25 F120
    G1 E5 F60
    G1 E1 F60
    G1 E-1 F60
    M400
    RESTORE_PRESSURE_ADVANCE
    RESTORE_GCODE_STATE NAME=__filament__load
  {% else %}
    LOG_ERROR MSG="temperature too low - skipping FILAMENT_LOAD"
  {% endif %}


[gcode_macro FILAMENT_PRIME]
description: slow prime
gcode:
  {% set mm = params.MM|default(5)|int %}
  SAVE_GCODE_STATE NAME=__filament__load
  NOTE_PRESSURE_ADVANCE
  SET_PRESSURE_ADVANCE ADVANCE=0
  M83
  G1 E{mm} F60
  G1 E1 F60
  G1 E-1 F60
  M400
  RESTORE_PRESSURE_ADVANCE
  RESTORE_GCODE_STATE NAME=__filament__load

[gcode_macro FILAMENT_UNLOAD]
description: fast unload 100mm of filament 
gcode:
  SAVE_GCODE_STATE NAME=__filament__load
  M83
  G1 E-45 F960
  G1 E-45 F960
  G1 E-10 F960
  RESTORE_GCODE_STATE NAME=__filament__load
