geoffrey-young/3D-Printing/klipper/voron/macros/drivers.cfg

[gcode_macro REDUCE_TMC_CURRENT]
gcode:
  SET_TMC_CURRENT STEPPER=stepper_x CURRENT=0.80
  SET_TMC_CURRENT STEPPER=stepper_y CURRENT=0.80


[gcode_macro RESTORE_TMC_CURRENT]
gcode:
  SET_TMC_CURRENT STEPPER=stepper_x CURRENT={ printer.configfile.config['tmc2209 stepper_x'].run_current }
  SET_TMC_CURRENT STEPPER=stepper_y CURRENT={ printer.configfile.config['tmc2209 stepper_y'].run_current }


[gcode_macro CURRENT_TMC_CURRENT]
gcode:
  M118 stepper_x run_current { printer['tmc2209 stepper_x'].run_current }
  M118 stepper_y run_current { printer['tmc2209 stepper_y'].run_current }
