geoffrey-young/3D-Printing/klipper/voron/2.4/afterburner.cfg

[extruder]
step_pin: PD5
dir_pin: !PD6
enable_pin: !PD4

## Bondtech LGX
# use either
#    gear_ratio: 45:14, 37:17
#    rotation_distance: 55
# or
#    rotation_distance: 8
# but not both!
rotation_distance: 8
microsteps: 16
full_steps_per_rotation: 200

nozzle_diameter: 0.400
filament_diameter: 1.75

heater_pin: PB15
sensor_type: ATC Semitec 104GT-2
sensor_pin: PC0
min_temp: 10
max_temp: 300
max_power: 1.0
min_extrude_temp: 170

pressure_advance: 0.048
pressure_advance_smooth_time: 0.040

[tmc2209 extruder]
uart_pin: PD7
interpolate: false
run_current: 0.5
hold_current: 0.4
sense_resistor: 0.110
stealthchop_threshold: 0


[probe]
pin: ^PA3
x_offset: 0
y_offset: 25.0
z_offset: 0
speed: 5.0
samples: 3
samples_result: median
sample_retract_dist: 3.0
samples_tolerance: 0.006
samples_tolerance_retries: 3


[heater_fan hotend_fan]
pin: PB0
max_power: 1.0
kick_start_time: 0.5
heater: extruder
heater_temp: 50.0
#fan_speed: 1.0

[fan]
pin: PB1
max_power: 1.0
kick_start_time: 0.5
off_below: 0.10
