geoffrey-young/3D-Printing/klipper/voron/macros/gantry.cfg

[gcode_macro QGL]
description: QGL
variable_skip: False
gcode:
  {% if skip %}
    M118 skipping QGL
    SKIP_QGL SKIP=False
    G90
  {% else %}
    STATUS_QGL_START
    M107
    BED_MESH_CLEAR
    BRUSH
    G28
    QUAD_GANTRY_LEVEL
    G28
    G90
    GET_POSITION
    STATUS_QGL_END
  {% endif %}


[gcode_macro CHECK_QGL]
description: only QGL if required
gcode:
  CHECK_HOMED
  {% if printer.quad_gantry_level.applied %}
    M118 QGL already applied - skipping...
    G90
  {% else %}
    SAFE_Z HOP=5
    QGL
  {% endif %}


[gcode_macro QUICK_QGL]
description: rough QGL - useful for simply making sure the nozzle won't hit the bed anywhere
gcode:
  M118 quick QGL...

  {% if printer.quad_gantry_level.applied %}
    M118 QGL already applied - skipping...
    G90
  {% else %}
    M107
    CHECK_HOMED
    STATUS_QGL_START
    QUAD_GANTRY_LEVEL RETRY_TOLERANCE=0.015 SAMPLES_TOLERANCE=0.006 SAMPLES_RESULT=average
    G28
    G90
    STATUS_READY
  {% endif %}


[gcode_macro SKIP_QGL]
description: skip QGLon next run
gcode:
  {% set skip = params.SKIP|default(True, True)|int %}

  SET_GCODE_VARIABLE MACRO=QGL VARIABLE=skip VALUE={skip}

  M118 { 'SKIP_QGL = %d' % (skip) }


[gcode_macro G32]
gcode:
  QGL


[gcode_macro RAISE_BACK]
description: attempt to offset rear gantry sag for easier QGL
gcode:
  M118 raising back...
  {% for i in range(params.TIMES | default(3) | int) %}
    FORCE_MOVE STEPPER=stepper_z1 DISTANCE=2 VELOCITY=5
    FORCE_MOVE STEPPER=stepper_z2 DISTANCE=2 VELOCITY=5
  {% endfor %}
  G28
