geoffrey-young/3D-Printing/klipper/voron/macros/mesh.cfg

[gcode_macro GENERATE_MESH]
description: use SKIP_MESH to decide whether to generate a mesh this run
variable_notify: False
variable_skip: False
gcode:
  {% set mesh = params.MESH | default('FULL') %}

  CHECK_QGL

  STATUS_MESH_START

  {% if skip %}
    {% if not printer['bed_mesh'].profile_name %}
      M118 mesh skip criteria not met
      {% set skip = False %}
    {% else %}
      {% set mesh = 'SKIP' %}
    {% endif %}
  {% endif %}

  {% if 'SKIP' in mesh and skip %}
    M118 skipping mesh generation...
  {% else %}

    STATUS_MESH_START

    NOTE_FAN
    M107

    M118 { 'generating %s mesh' % (mesh) }
    {% if 'FULL' in mesh %}
      FULL_BED_MESH
    {% elif 'FAST' in mesh %}
      FAST_BED_MESH
    {% elif 'EXTREME' in mesh %}
      EXTREME_BED_MESH
    {% else %}
      BED_MESH
    {% endif %}
  {% endif %}

  RESTORE_FAN

  STATUS_MESH_END

  SKIP_MESH SKIP=False  # if you want to skip you need to explicity do it each time

  {% if notify %}
    NOTIFY MSG="mesh complete"
    CLEAR_NOTIFY_AFTER_MESH
  {% endif %}


[gcode_macro NOTIFY_AFTER_MESH]
description: notify when mesh is complete
gcode:
  LOG_DEBUG MSG="will notify when mesh is complete..."
  SET_GCODE_VARIABLE MACRO=GENERATE_MESH VARIABLE=notify VALUE=1

[gcode_macro CLEAR_NOTIFY_AFTER_MESH]
description: clear mesh notify
gcode:
  SET_GCODE_VARIABLE MACRO=GENERATE_MESH VARIABLE=notify VALUE=0


[gcode_macro SKIP_MESH]
description: skip mesh on next run
gcode:
  {% set skip = params.SKIP|default(True, True)|int %}

  SET_GCODE_VARIABLE MACRO=GENERATE_MESH VARIABLE=skip VALUE={skip}

  {% if skip %}
    SET_GCODE_VARIABLE MACRO=QGL VARIABLE=skip VALUE={skip}
  {% endif %}

  M118 { 'SKIP_MESH = %d' % (skip) }


[gcode_macro FULL_BED_MESH]
description: generate 9x9 mesh
gcode:
  MESH_PREP
  M118 creating 9x9 bed mesh
  BED_MESH_CALIBRATE probe_count=9,9 relative_reference_index=40
  BRUSH_HOME


[gcode_macro FAST_BED_MESH]
description: generate 3x3 mesh with 1 sample
gcode:
  MESH_PREP
  M118 creating 3x3 bed mesh
  BED_MESH_CALIBRATE probe_count=3,3 relative_reference_index=4 samples=1 mesh_pps=4,4
  BRUSH_HOME


[gcode_macro BED_MESH]
description: generate default mesh
gcode:
  MESH_PREP
  M118 creating default (7x7) bed mesh
  BED_MESH_CALIBRATE
  BRUSH_HOME


[gcode_macro EXTREME_BED_MESH]
description: generate large, detailed mesh
gcode:
  MESH_PREP
  M118 creating 11x11 bed mesh
  BED_MESH_CALIBRATE probe_count=11,11 relative_reference_index=60 mesh_min="5,5" mesh_max="340,340"
  BRUSH_HOME


[gcode_macro DENSE_BED_MESH]
description: generate large, detailed mesh
gcode:
  MESH_PREP
  M118 creating 11x11 bed mesh
  BED_MESH_CALIBRATE probe_count=11,11 relative_reference_index=60
  BRUSH_HOME



[gcode_macro MESH_PREP]
description: BED_MESH_CLEAR and QGL before each new mesh
gcode:
  STATUS_OFF
  M107
  BED_MESH_CLEAR
  QGL
  BRUSH
  STATUS_MESH_START
