geoffrey-young/3D-Printing/klipper/voron/v2/hotends/rapido.cfg

#[include rapido/rapido-1.cfg]
[include rapido/rapido-2.cfg]


[gcode_macro HOTEND_INIT]
description: initialize hotend
variable_hotend: "rapido"
gcode:

  LOG_DEBUG MSG='{ "initializing %s hotend..." % (hotend) }'

  SET_GCODE_VARIABLE MACRO=RESTORE_CURRENT_NOZZLE VARIABLE=hotend VALUE='"{hotend}"'

  RESTORE_CURRENT_NOZZLE

  FORM_TIP_INIT


[gcode_macro FORM_TIP_INIT]
description: initialize toolhead parameters with proper tip forming values
gcode:

  M118 setting rapido tip forming variables...

  SET_GCODE_VARIABLE MACRO=FORM_TIP VARIABLE=home_position_to_nozzle VALUE=50
  SET_GCODE_VARIABLE MACRO=FORM_TIP VARIABLE=sensor_to_nozzle VALUE=0
  SET_GCODE_VARIABLE MACRO=FORM_TIP VARIABLE=extruder_to_nozzle VALUE=0

  SET_GCODE_VARIABLE MACRO=FORM_TIP VARIABLE=cooling_tube_length VALUE=22
  SET_GCODE_VARIABLE MACRO=FORM_TIP VARIABLE=cooling_tube_position VALUE=43
  SET_GCODE_VARIABLE MACRO=FORM_TIP VARIABLE=skinnydip_distance VALUE=40

  SET_GCODE_VARIABLE MACRO=FORM_TIP VARIABLE=cooling_moves VALUE=8
  SET_GCODE_VARIABLE MACRO=FORM_TIP VARIABLE=cooling_zone_pause VALUE=1000
  SET_GCODE_VARIABLE MACRO=FORM_TIP VARIABLE=dip_extraction_speed VALUE=70
  SET_GCODE_VARIABLE MACRO=FORM_TIP VARIABLE=dip_insertion_speed VALUE=33
  SET_GCODE_VARIABLE MACRO=FORM_TIP VARIABLE=final_cooling_speed VALUE=50
  SET_GCODE_VARIABLE MACRO=FORM_TIP VARIABLE=final_eject VALUE=0
  SET_GCODE_VARIABLE MACRO=FORM_TIP VARIABLE=initial_cooling_speed VALUE=10
  SET_GCODE_VARIABLE MACRO=FORM_TIP VARIABLE=melt_zone_pause VALUE=500
  SET_GCODE_VARIABLE MACRO=FORM_TIP VARIABLE=ramming_volume VALUE=2
  SET_GCODE_VARIABLE MACRO=FORM_TIP VARIABLE=ss_ramming VALUE=0
  SET_GCODE_VARIABLE MACRO=FORM_TIP VARIABLE=toolchange_temp VALUE=0
  SET_GCODE_VARIABLE MACRO=FORM_TIP VARIABLE=unloading_speed VALUE=20
  SET_GCODE_VARIABLE MACRO=FORM_TIP VARIABLE=unloading_speed_start VALUE=100
  SET_GCODE_VARIABLE MACRO=FORM_TIP VARIABLE=use_fast_skinnydip VALUE=0
  SET_GCODE_VARIABLE MACRO=FORM_TIP VARIABLE=use_skinnydip VALUE=1

  _FORM_TIP_SYNC
