geoffrey-young/3D-Printing/klipper/voron/v2/hotends/rapido/rapido-2.cfg

# rapido hf 2.0 - 20230630
# the one with the green heat sleeve :)

[extruder]
sensor_type: ATC Semitec 104NT-4-R025H42G
max_temp: 300

control = pid
pid_Kp=19.939
pid_Ki=1.621
pid_Kd=61.312
