geoffrey-young/3D-Printing/klipper/voron/v2/display.cfg

[display]
lcd_type: uc1701
cs_pin: PC11
a0_pin: PD2
rst_pin: PC10
encoder_pins: ^PC6,^PC7
click_pin: ^!PA8
contrast: 63
spi_software_mosi_pin: PA7
spi_software_miso_pin: PA6
spi_software_sclk_pin: PA5
menu_timeout:30

[neopixel fysetc_mini12864]
pin: PC12
chain_count: 3
initial_RED: 0.0
initial_GREEN: 0.0
initial_BLUE: 0.0
color_order: RGB

[delayed_gcode setdisplayneopixel]
initial_duration: 1
gcode:
    SET_LED LED=fysetc_mini12864 RED=0.25 GREEN=0.25 BLUE=0 INDEX=1 TRANSMIT=0
    SET_LED LED=fysetc_mini12864 RED=0.6 GREEN=0.25 BLUE=0 INDEX=2 TRANSMIT=0
    SET_LED LED=fysetc_mini12864 RED=0.6 GREEN=0.25 BLUE=0 INDEX=3 TRANSMIT=1


[gcode_macro RESET_DISPLAY_LEDS]
gcode:
  UPDATE_DELAYED_GCODE ID=setdisplayneopixel DURATION=1
