geoffrey-young/3D-Printing/klipper/voron/v2/hotends/rapido/rapido-1.cfg

# rapido hf 1.0

[extruder]
sensor_type: PT1000
max_temp: 310

control = pid
pid_Kp=20.627
pid_Ki=1.763
pid_Kd=60.334
