geoffrey-young/3D-Printing/klipper/voron/v2/probe.cfg

#[include probes/omron.cfg]
#[include probes/klicky.cfg]
[include probes/tap.cfg]


[probe]
pin: ^PA3
