geoffrey-young/3D-Printing/klipper/voron/macros/cleanup.cfg

[gcode_macro CLEANUP]
description: post-PRINT_END tidying
gcode:

  RESET_SKIPS

  DISABLE_FILAMENT_SENSOR

  BRUSH_PURGE_RESET

  CLEAR_PAUSE

  SET_IDLE_TIMEOUT TIMEOUT={printer.configfile.settings.idle_timeout.timeout}

  SET_VELOCITY_LIMIT VELOCITY={printer.configfile.settings.printer.max_velocity} ACCEL={printer.configfile.settings.printer.max_accel} ACCEL_TO_DECEL={printer.configfile.settings.printer.max_accel_to_decel}

  CONFIGURE_FINE_PRINT_TYPE_ACCEL

  STATUS_COMPLETE
