geoffrey-young/3D-Printing/klipper/voron/v2/ercf-hh.cfg

[include ercf-hh/ercf_parameters.cfg]
[include ercf-hh/ercf_hardware-ezbrd.cfg]
[include ercf-hh/ercf_software.cfg]
[include ercf-hh/macros/ercf.cfg]
[include ercf-hh/menu/ercf.cfg]


[pause_resume]
recover_velocity: 300.0

[extruder]
max_extrude_only_distance: 200
max_extrude_cross_section: 50.0
