geoffrey-young/3D-Printing/klipper/voron/macros/variables.cfg

[include save_variables/nozzles.cfg]


[save_variables]
filename: ~/klipper_config/.variables.txt


[gcode_macro DUMP_SAVE_VARIABLES]
description: dump klipper save variables
gcode:
  {% set svv = printer.save_variables.variables %}

  {% for k,v in svv|dictsort %}
    M118 { "found stored variable: %s => %s" % (k, v) }
  {% endfor %}


[gcode_macro DISPLAY_SAVE_VARIABLE]
description: macro shortcut for showing a saved variable
gcode:
  {% set key = params.KEY | default('') | string %}
  {% set svv = printer.save_variables.variables %}

  {% if key %}
    M118 stored variable {key} is {svv[key]}
  {% endif %}
