geoffrey-young/3D-Printing/klipper/voron/macros/util/config.cfg

[gcode_macro DUMP_CONFIG]
description: dump printer variables
gcode:
 {% for name1 in printer %}
    {% for name2 in printer[name1] %}
       M118 { "DUMP: printer['%s'].%s = %s" % (name1, name2, printer[name1][name2]) }
    {% else %}
       M118 { "DUMP: printer['%s'] = %s" % (name1, printer[name1]) }
    {% endfor %}
 {% endfor %}
