geoffrey-young/3D-Printing/klipper/voron/v2/ercf-hh/macros/calibration.cfg

[gcode_macro ER_CALIBRATE_TOOL]
gcode:
  {% set tool = params.TOOL | default(8,True) | int %}
  {% if tool == 0 %}
    M118 don't want to calibrate tool 0, right?
  {% else %}
    M118 calibrating tool T{tool}...
    M104 S245
    ERCF_HOME FORCE_UNLOAD=1 PRELOAD=0
    ER_RAISE_ERROR_IF_PAUSED
    CENTER
    ER_GOTO_LOAD_POSITION
    M109 S245
    ERCF_CALIBRATE_SINGLE TOOL={tool}
    ER_RAISE_ERROR_IF_PAUSED
    ERCF_HOME PRELOAD=0
    ER_RAISE_ERROR_IF_PAUSED
    ERCF_SELECT TOOL={tool}
    ER_RAISE_ERROR_IF_PAUSED
    ERCF_LOAD
    ER_RAISE_ERROR_IF_PAUSED
    ERCF_CALIBRATE_ENCODER RANGE=2 DIST=1000
    ER_RAISE_ERROR_IF_PAUSED
    ERCF_HOME PRELOAD=0
    ER_RAISE_ERROR_IF_PAUSED
    CENTER
    ER_GOTO_LOAD_POSITION
    T{tool}
    ER_RAISE_ERROR_IF_PAUSED
    ERCF_EJECT
    ER_RAISE_ERROR_IF_PAUSED
  {% endif %}


[gcode_macro ER_CALIBRATE_BLOCK]
gcode:
  {% set tool = params.TOOL | default(8,True) | int %}
  M118 calibrating block T{tool}...
  ERCF_HOME
  {% if tool > 3 %}
    ERCF_SELECT TOOL=1
  {% else %}
    ERCF_SELECT TOOL=7
  {% endif %}
  ERCF_SELECT TOOL={tool}
  ERCF_LOAD
  ERCF_SERVO_UP
  ERCF_MOTORS_OFF
  SET_GCODE_VARIABLE MACRO=ER_CALIBRATE_BLOCK_END VARIABLE=tool VALUE={tool}
  M118 now run ER_CALIBRATE_BLOCK_END


[gcode_macro ER_CALIBRATE_BLOCK_END]
variable_tool: 8
gcode:
  {% set tool = params.TOOL | default(printer['gcode_macro ER_CALIBRATE_BLOCK_END']['tool']) | int %}
  ERCF_CALIBRATE_SELECTOR TOOL={tool}
  ERCF_HOME


[gcode_macro ER_TEST_BLOCK_LOAD]
gcode:
  {% set tool = params.TOOL | default(8,True) | int %}

  {% for i in range(3) %}
    S0
    S8
    P{tool}
    M400
    G4 P1000
  {% endfor %}


[gcode_macro ER_CALIBRATE_ENCODER]
gcode:
  ERCF_HOME FORCE_UNLOAD=1 PRELOAD=1 TOOL=0
  ERCF_CALIBRATE_ENCODER DIST=1000
  ERCF_EJECT
  ERCF_RESET
  ERCF_HOME
