geoffrey-young/3D-Printing/klipper/voron/v2/extras/adxl.cfg

[mcu rpi]
serial: /tmp/klipper_host_mcu

[adxl345]
cs_pin: rpi:None
axes_map: -z,-y,-x

[resonance_tester]
accel_chip: adxl345
probe_points:
    173,175,30
max_freq: 80


[input_shaper]
shaper_freq_x: 52.4
shaper_type_x: mzv
damping_ratio_x: 0.053
shaper_freq_y: 32.8
shaper_type_y: mzv
damping_ratio_y: 0.074


[gcode_macro SET_SHAPER_ZV]
description: set zv input shaper
gcode:
  SET_INPUT_SHAPER SHAPER_FREQ_X=51.8 SHAPER_FREQ_Y=38.2 SHAPER_TYPE_X=zv SHAPER_TYPE_Y=zv
  SET_GCODE_VARIABLE MACRO=RESTORE_INPUT_SHAPER VARIABLE=shaper VALUE="zv"
  M118 set input shaper zv


[gcode_macro SET_SHAPER_ZVD]
description: set zvd input shaper
gcode:
  SET_INPUT_SHAPER SHAPER_FREQ_X=59.4 SHAPER_FREQ_Y=44.4 SHAPER_TYPE_X=zvd SHAPER_TYPE_Y=zvd
  SET_GCODE_VARIABLE MACRO=RESTORE_INPUT_SHAPER VARIABLE=shaper VALUE="zvd"
  M118 set input shaper zvd


[gcode_macro SET_SHAPER_EI]
description: set ei input shaper
gcode:
  SET_INPUT_SHAPER SHAPER_FREQ_X=62.6 SHAPER_FREQ_Y=44.2 SHAPER_TYPE_X=ei SHAPER_TYPE_Y=ei
  SET_GCODE_VARIABLE MACRO=RESTORE_INPUT_SHAPER VARIABLE=shaper VALUE="ei"
  M118 set input shaper ei


[gcode_macro RESTORE_INPUT_SHAPER]
description: restore default input shaper
variable_shaper: "mzv"
gcode:
  {% set is = printer.configfile.settings.input_shaper %}
  SET_INPUT_SHAPER SHAPER_FREQ_X={is.shaper_freq_x} SHAPER_FREQ_Y={is.shaper_freq_y} SHAPER_TYPE_X={is.shaper_type_x} SHAPER_TYPE_Y={is.shaper_type_y} DAMPING_RATIO_X={is.damping_ratio_x} DAMPING_RATIO_Y={is.damping_ratio_y}
  SET_GCODE_VARIABLE MACRO=RESTORE_INPUT_SHAPER VARIABLE=shaper VALUE="'{is.shaper_type_x}'"
  M118 restored default input shaper {is.shaper_type_x}
