geoffrey-young/3D-Printing/klipper/voron/macros/util/shell.cfg

# https://github.com/th33xitus/kiauh/blob/master/resources/gcode_shell_command.py

[gcode_macro NOTIFY]
description: call shell notify routine
gcode:
  {% set msg = params.MSG|default("default message?")|string %}
  {% set error = params.ERROR|default(0, True)|int %}
  {% if error %}
    RESPOND MSG="{msg}" TYPE=error
  {% endif %}
  RUN_SHELL_COMMAND CMD=notify PARAMS={msg|tojson}


[gcode_macro ERROR_NOTIFY]
description: notify only if it looks like an error
gcode:
  {% if "error" in printer.print_stats.state and "xyz" in printer.toolhead.homed_axes %}
    {% set msg = "ERROR printing %s: %s" % (printer.print_stats.filename.split('/')[-1], printer.print_stats.message) | string %}
    NOTIFY MSG="{msg}" ERROR=1
  {% endif %}


[gcode_shell_command notify]
command: bash /home/pi/notify.bash
timeout: 5
verbose: False


[gcode_macro SHUTDOWN]
description: call shell shutdown
gcode:
  M118 shutting down...
  RUN_SHELL_COMMAND CMD=shutdown
  {action_call_remote_method("shutdown_machine")}


[gcode_shell_command shutdown]
command: bash /home/pi/shutdown.bash
timeout: 5
verbose: False
