geoffrey-young/3D-Printing/klipper/voron/v2/probes/klicky/z_calibration.cfg

[z_calibration]
probe_nozzle_x: 236
probe_nozzle_y: 349

probe_switch_x: 232
probe_switch_y: 330

#switch_offset: 0.50    # smaller values == farther from bed
#switch_offset: 0.42    # omron
#switch_offset: 0.46    # generic
switch_offset: 0.48

max_deviation: 1.6

probing_first_fast: true

start_gcode: Dock_Probe_Unlock
before_switch_gcode: Attach_Probe
end_gcode: Dock_Probe


# using a value other than 0 seems to confuse CALIBRATE_Z 
# on multiple BED_MESH_CLEAR + QGL + BED_MESH_CALIBRATE cycles
#
# also note, this overrides any SAVE_CONFIG in printer.cfg
[stepper_z]
position_endstop = 0.0


[gcode_macro AUTO_CALIBRATE_Z]
description: klicky auto-z routine
variable_skip: False
gcode:
  {% if skip %}
    M118 skiping AUTO_CALIBRATE_Z
    SKIP_AUTO_CALIBRATE_Z SKIP=False
  {% else %}
    M118 calculating z offset...
    STATUS_AUTO_Z_START
    M107
    DOCK_PROBE
    BRUSH TIMES=3 RETRACT=1
    CALIBRATE_Z
    GET_POSITION
    DISPLAY_Z
    STATUS_AUTO_Z_END
    AUTO_Z_SANITY_CHECK
    STORE_Z_OFFSET
  {% endif %}


[gcode_macro SKIP_AUTO_CALIBRATE_Z]
description: skip auto z calibrate
gcode:
  {% set skip = params.SKIP|default(True, True)|int %}

  SET_GCODE_VARIABLE MACRO=AUTO_CALIBRATE_Z VARIABLE=skip VALUE={skip}

  M118 { 'SKIP_AUTO_CALIBRATE_Z = %d' % (skip) }


[gcode_macro HOME_SWITCH]
gcode:
  {% set x  = printer['configfile'].config['z_calibration']["probe_switch_x"]|float %}
  {% set y  = printer['configfile'].config['z_calibration']["probe_switch_y"]|float %}

  {% set msg = "switch body located at X%0.1f Y%0.1f" % (x,y) %}

  M118 { msg }

  CHECK_QGL

  Attach_Probe

  SAVE_GCODE_STATE NAME=__locate
  G90
  G1 X{x} Y{y}
  G1 Z8 F600
  RESTORE_GCODE_STATE NAME=__locate


[gcode_macro HOME_NOZZLE]
gcode:
  {% set x  = printer['configfile'].config['z_calibration']["probe_nozzle_x"]|float %}
  {% set y  = printer['configfile'].config['z_calibration']["probe_nozzle_y"]|float %}

  {% set msg = "nozzle located at X%0.1f Y%0.1f" % (x,y) %}

  M118 { msg }

  CHECK_QGL

  Dock_Probe

  SAVE_GCODE_STATE NAME=__locate
  G90
  G1 X{x} Y{y}
  G1 Z2 F600
  RESTORE_GCODE_STATE NAME=__locate
